HadesVR/HadesVR/docs/img/1.jpg

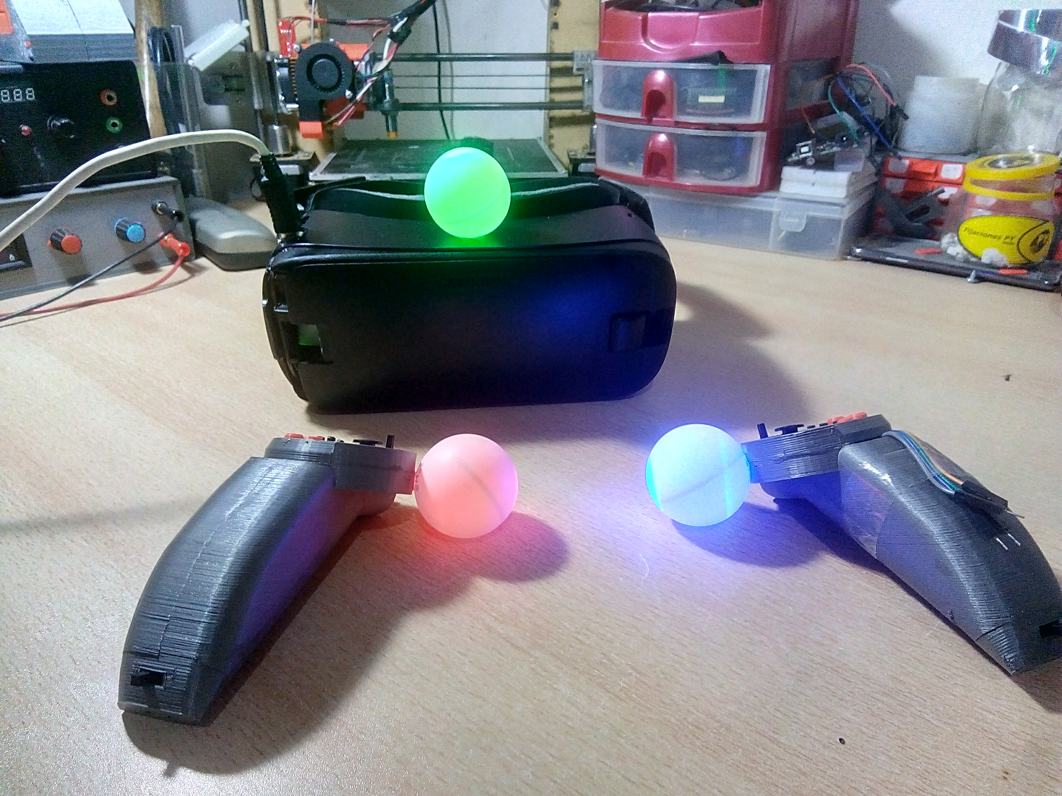
docs/img/1.jpg
