HadesVR/HadesVR/docs/img/2.jpg

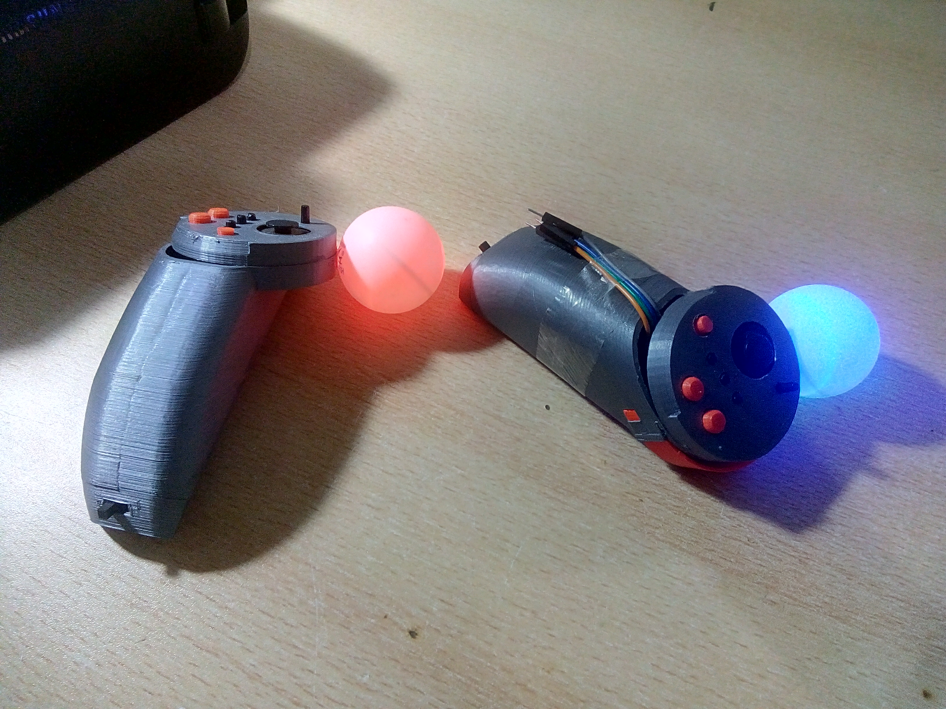
docs/img/2.jpg
