HadesVR/HadesVR/Software/Firmware/Controller_INDEX/Left_controller/Left_controller.ino

/*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
  The above copyright notice and this permission notice shall be included in all copies or substantial portions of the Software.

  THE SOFTWARE IS PROVIDED "AS IS", WITHOUT WARRANTY OF ANY KIND, EXPRESS OR IMPLIED,INCLUDING BUT NOT LIMITED TO
  THE WARRANTIES OF MERCHANTABILITY, FITNESS FOR A PARTICULAR PURPOSE AND NONINFRINGEMENT. IN NO EVENT SHALL THE
  AUTHORS OR COPYRIGHT HOLDERS BE LIABLE FOR ANY CLAIM, DAMAGES OR OTHER LIABILITY, WHETHER IN AN ACTION OF CONTRACT,
  TORT OR OTHERWISE, ARISING FROM, OUT OF OR IN CONNECTION WITH THE SOFTWARE OR THE USE OR OTHER DEALINGS IN THE SOFTWARE.
*/

#include <Wire.h>
#include <SPI.h>
#include <EEPROM.h>
#include "RF24.h"
#include "RegisterMap.h"

//==========================================================================================================
//************************************ USER CONFIGURABLE STUFF HERE*****************************************
//==========================================================================================================

#define MPU9250_ADDRESS     0x68            //ADO 0
#define CALPIN              5               //pin to start mag calibration at power on

#define APin                4
#define BPin                3
#define SysPin              5
#define FingerIndexPin      1
#define FingerMiddlePin     6
#define FingerRingPin       7
#define FingerPinkyPin      8
#define TrackpadPin         A0
#define JoyXPin             A1
#define JoyYPin             A2
#define JoyClickPin         2
#define TriggerPin          A3
#define VbatPin             A6

#define BatLevelMax         968             //you need to find all of these values on your own
#define JoyXMin             200             //check on the utils folder for sketches and instructions
#define JoyXMax             900             //that help on getting these values
#define JoyYMin             150             //YOU NEED TO DO THIS FOR BOTH CONTROLLERS
#define JoyYMax             870             //if you use these values without changing them you MAY
#define JoyXDeadZoneMin     515             //get stick drift
#define JoyXDeadZoneMax     590
#define JoyYDeadZoneMin     430
#define JoyYDeadZoneMax     560

//uint64_t Pipe = 0xF0F0F0F0E1LL; //right
uint64_t Pipe = 0xF0F0F0F0D2LL; //left
//==========================================================================================================


float magCalibration[3]; // factory mag calibration

struct Calibration {
  int calDone;
  float magBias[3];
  float magScale[3];
};
bool calDone;
Calibration cal;


static int ret;
static uint8_t fifoCount = 0;
struct s_quat {
  float w, x, y, z;
};

union u_quat {
  struct s_quat _f;
  long _l[4];
} q;

float magQuat[4] {1, 0, 0, 0};
float magHDG = 0;
float dmpHDG = 0;
float offsetHDG = 0;
float DMPquat[4];

static float mx, my, mz;
static short ax, ay, az;

enum class MFS { M14BITS, M16BITS }; // 0.6mG, 0.15mG per LSB
static float mRes;
MFS MFSSEL = MFS::M16BITS;

#define DMP_CODE_SIZE           (3062)
#define STARTADDRESS            0x0400
#define DMP_SAMPLE_RATE         (200)
const unsigned char dmp_memory[DMP_CODE_SIZE] PROGMEM = {
  /* bank # 0 */
  0x00, 0x00, 0x70, 0x00, 0x00, 0x00, 0x00, 0x24, 0x00, 0x00, 0x00, 0x02, 0x00, 0x03, 0x00, 0x00,
  0x00, 0x65, 0x00, 0x54, 0xff, 0xef, 0x00, 0x00, 0xfa, 0x80, 0x00, 0x0b, 0x12, 0x82, 0x00, 0x01,
  0x03, 0x0c, 0x30, 0xc3, 0x0e, 0x8c, 0x8c, 0xe9, 0x14, 0xd5, 0x40, 0x02, 0x13, 0x71, 0x0f, 0x8e,
  0x38, 0x83, 0xf8, 0x83, 0x30, 0x00, 0xf8, 0x83, 0x25, 0x8e, 0xf8, 0x83, 0x30, 0x00, 0xf8, 0x83,
  0xff, 0xff, 0xff, 0xff, 0x0f, 0xfe, 0xa9, 0xd6, 0x24, 0x00, 0x04, 0x00, 0x1a, 0x82, 0x79, 0xa1,
  0x00, 0x00, 0x00, 0x3c, 0xff, 0xff, 0x00, 0x00, 0x00, 0x10, 0x00, 0x00, 0x38, 0x83, 0x6f, 0xa2,
  0x00, 0x3e, 0x03, 0x30, 0x40, 0x00, 0x00, 0x00, 0x02, 0xca, 0xe3, 0x09, 0x3e, 0x80, 0x00, 0x00,
  0x20, 0x00, 0x00, 0x00, 0x00, 0x00, 0x00, 0x00, 0x40, 0x00, 0x00, 0x00, 0x60, 0x00, 0x00, 0x00,
  0x00, 0x0c, 0x00, 0x00, 0x00, 0x0c, 0x18, 0x6e, 0x00, 0x00, 0x06, 0x92, 0x0a, 0x16, 0xc0, 0xdf,
  0xff, 0xff, 0x02, 0x56, 0xfd, 0x8c, 0xd3, 0x77, 0xff, 0xe1, 0xc4, 0x96, 0xe0, 0xc5, 0xbe, 0xaa,
  0x00, 0x00, 0x00, 0x00, 0xff, 0xff, 0x0b, 0x2b, 0x00, 0x00, 0x16, 0x57, 0x00, 0x00, 0x03, 0x59,
  0x40, 0x00, 0x00, 0x00, 0x00, 0x00, 0x1d, 0xfa, 0x00, 0x02, 0x6c, 0x1d, 0x00, 0x00, 0x00, 0x00,
  0x3f, 0xff, 0xdf, 0xeb, 0x00, 0x3e, 0xb3, 0xb6, 0x00, 0x0d, 0x22, 0x78, 0x00, 0x00, 0x2f, 0x3c,
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
  radio.setPayloadSize(32);
  radio.setPALevel(RF24_PA_LOW);
  radio.setDataRate(RF24_2MBPS);
  radio.openWritingPipe(Pipe);
  radio.startListening();
  radio.setAutoAck(false);

  Wire.begin();

  if (readByte(MPU9250_ADDRESS, WHO_AM_I_MPU9250) == MPU9250_WHOAMI_DEFAULT_VALUE)
  {

    Serial.println("MPU9250 is online");
    initMPU();
    initDMP();
    if (readByte(AK8963_ADDRESS, AK8963_WHO_AM_I) == AK8963_WHOAMI_DEFAULT_VALUE)
    {
      Serial.println("AK8963 is online");
      initAK8963(magCalibration);
    }
    else
    {
      Serial.print("Could not connect to AK8963: 0x");
      Serial.println(readByte(AK8963_ADDRESS, AK8963_WHO_AM_I), HEX);
    }
  }
  else
  {
    Serial.print("Could not connect to MPU9250: 0x");
    Serial.println(readByte(MPU9250_ADDRESS, WHO_AM_I_MPU9250), HEX);
    while (true) {
      //      digitalWrite(PC13, LOW);
      delay(200);
      //     digitalWrite(PC13, HIGH);
      delay(200);
      //     digitalWrite(PC13, LOW);
      delay(200);
      //     digitalWrite(PC13, HIGH);
      delay(1000);
    }
  }

  EEPROM.get(0, cal);

  calDone = (cal.calDone != 99);                                  //check if calibration values are on flash
  while (calDone) {
    delay(200);
    if (!digitalRead(CALPIN)) {
      calDone = false;
    }
  }

  if (!digitalRead(CALPIN)) {                                        //enter calibration mode
    Serial.println("Magnetic calibration mode.");
    delay(1000);
    //    digitalWrite(PC13, LOW);
    magcalMPU9250(cal.magBias, cal.magScale);
    //    digitalWrite(PC13, HIGH);
    Serial.print("magBias: "); Serial.print(cal.magBias[0], 7); Serial.print(","); Serial.print(cal.magBias[1], 7); Serial.print(","); Serial.println(cal.magBias[2], 7);
    Serial.print("magScale: "); Serial.print(cal.magScale[0], 7); Serial.print(","); Serial.print(cal.magScale[1], 7); Serial.print(","); Serial.println(cal.magScale[2], 7);

    Serial.println("Writting calibration values to EEPROM!");
    cal.calDone = 99;
    EEPROM.put(0, cal);
    delay(3000);
  }

  //initialize controller data.
  data.qW = 1;
  data.qX = 0;
  data.qY = 0;
  data.qZ = 0;
  data.BTN = 0;
  data.trigg = 0;
  data.axisX = 0;
  data.axisY = 0;
  data.trackY = 0;
  data.vBAT = 0;
  data.fingerThumb = 0;
  data.fingerIndex = 0;
  data.fingerMiddle = 0;
  data.fingerRing = 0;
  data.fingerPinky = 0;
  data.Data = 0x633;

  /*
    data.Data |= 0x03;  //non diy index controller identifier
    data.Data |= 0x10;  //controller reports accelerometer values
    data.Data |= 0x20;  //controller does support hand tracking
    //data.Data |= 0x40;  //handtracking type is analog
    data.Data |= 0x200;  //controller color is blue (80 for blue 100 for green 200 for red)
    data.Data |= 0x400; //controller reports battery %
  */

}

void loop() {

  updateMPU();

  //Serial.print("qw: "); Serial.print(q._f.w); Serial.print(" qx: "); Serial.print(q._f.x); Serial.print(" qy: "); Serial.print(q._f.y); Serial.print(" qz: "); Serial.println(q._f.z);
  joyTouch = false;
  int btn = 0;
  tracky = analogRead(TrackpadPin);
  if (tracky > 560) {
    trackoutput = 1;
    btn |= IB_TrackpadTouch;
  }
  if (tracky < 300 && tracky > 100) {
    trackoutput = 0;
    btn |= IB_TrackpadTouch;
  }
  if (tracky == 0) {
    trackoutput = -1;
    btn |= IB_TrackpadTouch;
  }
  if (tracky < 550 && tracky > 400) {
    trackoutput = 0;
  }

  axisX = analogRead(JoyXPin);
  axisY = analogRead(JoyYPin);

  if (axisX > JoyXDeadZoneMax || axisX < JoyXDeadZoneMin) {
    data.axisX = map(axisX, JoyXMin, JoyXMax, -127, 127);
    btn |= IB_ThumbStickTouch;
    joyTouch = true;
  } else {
    data.axisX = 0;
  }

  if (axisY > JoyYDeadZoneMax || axisY < JoyYDeadZoneMin) {
    data.axisY = -map(axisY, JoyYMin, JoyYMax, -127, 127);
    btn |= IB_ThumbStickTouch;
    joyTouch = true;
  } else {
    data.axisY = 0;
  }


  if (analogRead(TriggerPin) < 1000) {
    data.trigg = map(analogRead(TriggerPin), 1024, 0, 0, 255);
    data.fingerIndex = map(analogRead(TriggerPin), 1024, 0, 0, 255);
  }
  else {
    data.trigg = 0;
    data.fingerIndex = 0;
  }


  if (!digitalRead(APin)) {
    btn |= IB_AClick;
    btn |= IB_ATouch;
  }
  if (!digitalRead(BPin)) {
    btn |= IB_BClick;
    btn |= IB_BTouch;
  }
  if (!digitalRead(SysPin)) {
    btn |= IB_SYSClick;
  }
  if (!digitalRead(JoyClickPin)) {
    btn |= IB_ThumbStickClick;
  }
  //  if (digitalRead(FingerIndexPin)) {
  //    data.fingerIndex = 255;
  //  }
  //  else {
  //    data.fingerIndex = 0;
  //  }
  if (digitalRead(FingerMiddlePin)) {
    data.fingerMiddle = 255;
  }
  else {
    data.fingerMiddle = 0;
  }
  if (digitalRead(FingerRingPin)) {
    data.fingerRing = 255;
  }
  else {
    data.fingerRing = 0;
  }
  if (digitalRead(FingerPinkyPin)) {
    data.fingerPinky = 255;
  }
  else {
    data.fingerPinky = 0;
  }


  data.BTN = btn;
  data.trackY = (trackoutput * 127);
  data.vBAT = (map(analogRead(VbatPin), 787, BatLevelMax, 0, 255));
  data.qW = (int16_t)(q._f.w * 32767.f);
  data.qX = (int16_t)(q._f.y * 32767.f);
  data.qY = (int16_t)(q._f.z * 32767.f);
  data.qZ = (int16_t)(q._f.x * 32767.f);
  data.accX = ax;
  data.accY = ay;
  data.accZ = az;
  radio.stopListening();
  radio.write(&data, sizeof(ctrlData));
  radio.startListening();
}


void initMPU()
{
  unsigned char data;
  // reset device
  writeByte(MPU9250_ADDRESS, PWR_MGMT_1, 0x80);
  // wake up device
  writeByte(MPU9250_ADDRESS, PWR_MGMT_1, 0x00); // Clear sleep mode bit (6), enable all sensors
  delay(100); // Wait for all registers to reset

  writeByte(MPU9250_ADDRESS, MPU_CONFIG, 0x03); //set lpf to 42hz

  // get stable time source
  writeByte(MPU9250_ADDRESS, PWR_MGMT_1, 0x01);  // Auto select clock source to be PLL gyroscope reference if ready else
  delay(200);

  //enable all sensors
  writeByte(MPU9250_ADDRESS, PWR_MGMT_2, 0x00);
  delay(200);

  data = 3 << 3; // 11 = 2000dps
  writeByte(MPU9250_ADDRESS, GYRO_CONFIG, data);

  data = 1 << 3; // 01 = 4g
  writeByte(MPU9250_ADDRESS, ACCEL_CONFIG, data);
  // Set sample rate = gyroscope output rate/(1 + SMPLRT_DIV)
  writeByte(MPU9250_ADDRESS, SMPLRT_DIV, 0x04);  // Use a 200 Hz rate; a rate consistent with the filter update rate


  data = 0x01;          //BIT_DRDY_EN
  writeByte(MPU9250_ADDRESS, INT_ENABLE, data);
  // Configure Interrupts and Bypass Enable
  // Set interrupt pin active high, push-pull, hold interrupt pin level HIGH until interrupt cleared,
  // clear on read of INT_STATUS, and enable I2C_BYPASS_EN so additional chips
  // can join the I2C bus and all can be controlled by the Arduino as master
  writeByte(MPU9250_ADDRESS, INT_PIN_CFG, 0x22);
  delay(100);
}

void initDMP()
{
  dmpLoadFirmware(DMP_CODE_SIZE, dmp_memory, STARTADDRESS, DMP_SAMPLE_RATE);
  ret = dmp_set_fifo_rate(200);
  ret = enableDMP();
  ret = dmp_enable_features();
}

void initAK8963(float * destination)
{
  // First extract the factory calibration for each magnetometer axis
  uint8_t rawData[3];  // x/y/z gyro calibration data stored here
  writeByte(AK8963_ADDRESS, AK8963_CNTL, 0x00); // Power down magnetometer
  delay(10);
  writeByte(AK8963_ADDRESS, AK8963_CNTL, 0x0F); // Enter Fuse ROM access mode
  delay(10);
  readBytes(AK8963_ADDRESS, AK8963_ASAX, 3, &rawData[0]);  // Read the x-, y-, and z-axis calibration values
  destination[0] =  (float)(rawData[0] - 128) / 256. + 1.; // Return x-axis sensitivity adjustment values, etc.
  destination[1] =  (float)(rawData[1] - 128) / 256. + 1.;
  destination[2] =  (float)(rawData[2] - 128) / 256. + 1.;
  writeByte(AK8963_ADDRESS, AK8963_CNTL, 0x00); // Power down magnetometer
  delay(10);
  // Configure the magnetometer for continuous read and highest resolution
  // set Mscale bit 4 to 1 (0) to enable 16 (14) bit resolution in CNTL register,
  // and enable continuous mode data acquisition Mmode (bits [3:0]), 0010 for 8 Hz and 0110 for 100 Hz sample rates
  writeByte(AK8963_ADDRESS, AK8963_CNTL, (uint8_t)MFSSEL << 4 | Mmode); // Set magnetometer data resolution and sample ODR
  delay(10);

  //  Serial.println("Calibration values: ");
  //  Serial.print("X-Axis sensitivity adjustment value "); Serial.println(destination[0], 2);
  //  Serial.print("Y-Axis sensitivity adjustment value "); Serial.println(destination[1], 2);
  //  Serial.print("Z-Axis sensitivity adjustment value "); Serial.println(destination[2], 2);
  //  Serial.print("X-Axis sensitivity offset value "); Serial.println(cal.magBias[0], 2);
  //  Serial.print("Y-Axis sensitivity offset value "); Serial.println(cal.magBias[1], 2);
  //  Serial.print("Z-Axis sensitivity offset value "); Serial.println(cal.magBias[2], 2);
}

void magcalMPU9250(float * dest1, float * dest2)
{
  uint16_t ii = 0, sample_count = 0;
  int32_t mag_bias[3] = {0, 0, 0}, mag_scale[3] = {0, 0, 0};
  int16_t mag_max[3] = { -32767, -32767, -32767}, mag_min[3] = {32767, 32767, 32767}, mag_temp[3] = {0, 0, 0};

  Serial.println("Mag Calibration: Wave device in a figure eight until done!");
  delay(4000);

  // shoot for ~fifteen seconds of mag data
  if      (Mmode == 0x02) sample_count = 128;  // at 8 Hz ODR, new mag data is available every 125 ms
  else if (Mmode == 0x06) sample_count = 1500;  // at 100 Hz ODR, new mag data is available every 10 ms

  for (ii = 0; ii < sample_count; ii++)
  {
    uint8_t rawData[7];  // x/y/z gyro register data, ST2 register stored here, must read ST2 at end of data acquisition
    if (readByte(AK8963_ADDRESS, AK8963_ST1) & 0x01) { // wait for magnetometer data ready bit to be set
      readBytes(AK8963_ADDRESS, AK8963_XOUT_L, 7, &rawData[0]);  // Read the six raw data and ST2 registers sequentially into data array
      uint8_t c = rawData[6]; // End data read by reading ST2 register
      if (!(c & 0x08)) { // Check if magnetic sensor overflow set, if not then report data
        mag_temp[0] = ((int16_t)rawData[1] << 8) | rawData[0];  // Turn the MSB and LSB into a signed 16-bit value
        mag_temp[1] = ((int16_t)rawData[3] << 8) | rawData[2];  // Data stored as little Endian
        mag_temp[2] = ((int16_t)rawData[5] << 8) | rawData[4];
      }
    }
    for (int jj = 0; jj < 3; jj++)
    {
      if (mag_temp[jj] > mag_max[jj]) mag_max[jj] = mag_temp[jj];
      if (mag_temp[jj] < mag_min[jj]) mag_min[jj] = mag_temp[jj];
    }
    if (Mmode == 0x02) delay(135); // at 8 Hz ODR, new mag data is available every 125 ms
    if (Mmode == 0x06) delay(12); // at 100 Hz ODR, new mag data is available every 10 ms
  }
  //
  //  Serial.println("mag x min/max:"); Serial.println(mag_max[0]); Serial.println(mag_min[0]);
  //  Serial.println("mag y min/max:"); Serial.println(mag_max[1]); Serial.println(mag_min[1]);
  //  Serial.println("mag z min/max:"); Serial.println(mag_max[2]); Serial.println(mag_min[2]);

  // Get hard iron correction
  mag_bias[0]  = (mag_max[0] + mag_min[0]) / 2; // get average x mag bias in counts
  mag_bias[1]  = (mag_max[1] + mag_min[1]) / 2; // get average y mag bias in counts
  mag_bias[2]  = (mag_max[2] + mag_min[2]) / 2; // get average z mag bias in counts

  dest1[0] = (float) mag_bias[0] * mRes * magCalibration[0]; // save mag biases in G for main program
  dest1[1] = (float) mag_bias[1] * mRes * magCalibration[1];
  dest1[2] = (float) mag_bias[2] * mRes * magCalibration[2];

  // Get soft iron correction estimate
  mag_scale[0]  = (mag_max[0] - mag_min[0]) / 2; // get average x axis max chord length in counts
  mag_scale[1]  = (mag_max[1] - mag_min[1]) / 2; // get average y axis max chord length in counts
  mag_scale[2]  = (mag_max[2] - mag_min[2]) / 2; // get average z axis max chord length in counts

  float avg_rad = mag_scale[0] + mag_scale[1] + mag_scale[2];
  avg_rad /= 3.0;

  dest2[0] = avg_rad / ((float)mag_scale[0]);
  dest2[1] = avg_rad / ((float)mag_scale[1]);
  dest2[2] = avg_rad / ((float)mag_scale[2]);

  Serial.println("Mag Calibration done!");

  //  Serial.println("AK8963 mag biases (mG)");
  //  Serial.print(cal.magBias[0]); Serial.print(", ");
  //  Serial.print(cal.magBias[1]); Serial.print(", ");
  //  Serial.print(cal.magBias[2]); Serial.println();
  //  Serial.println("AK8963 mag scale (mG)");
  //  Serial.print(cal.magScale[0]); Serial.print(", ");
  //  Serial.print(cal.magScale[1]); Serial.print(", ");
  //  Serial.print(cal.magScale[2]); Serial.println();
}

void updateMag()
{
  if (readByte(AK8963_ADDRESS, AK8963_ST1) & 0x01) {             // wait for magnetometer data ready bit to be set
    int16_t magCount[3] = {0, 0, 0};                             // Stores the 16-bit signed magnetometer sensor output
    uint8_t rawData[7];                                          // x/y/z gyro register data, ST2 register stored here, must read ST2 at end of data acquisition
    readBytes(AK8963_ADDRESS, AK8963_XOUT_L, 7, &rawData[0]);    // Read the six raw data and ST2 registers sequentially into data array
    uint8_t c = rawData[6];                                      // End data read by reading ST2 register
    if (!(c & 0x08)) {                                           // Check if magnetic sensor overflow set, if not then report data
      magCount[0] = ((int16_t)rawData[1] << 8) | rawData[0];     // Turn the MSB and LSB into a signed 16-bit value
      magCount[1] = ((int16_t)rawData[3] << 8) | rawData[2];     // Data stored as little Endian
      magCount[2] = ((int16_t)rawData[5] << 8) | rawData[4];
    }

    // getMres();
    // Calculate the magnetometer values in milliGauss
    // Include factory calibration per data sheet and user environmental corrections

    mx = (float)(magCount[0] * mRes * magCalibration[0] - cal.magBias[0]) * cal.magScale[0];  // get actual magnetometer value, this depends on scale being set
    my = (float)(magCount[1] * mRes * magCalibration[1] - cal.magBias[1]) * cal.magScale[1];
    mz = (float)(magCount[2] * mRes * magCalibration[2] - cal.magBias[2]) * cal.magScale[2];

  }
}

float getMres()
{
  switch (MFSSEL)
  {
    // Possible magnetometer scales (and their register bit settings) are:
    // 14 bit resolution (0) and 16 bit resolution (1)
    // Proper scale to return milliGauss
    case MFS::M14BITS: return 10. * 4912. / 8190.0;
    case MFS::M16BITS: return 10. * 4912. / 32760.0;
  }
}

void mpu_reset_fifo()
{
  unsigned char data;

  data = 0;

  //reset registers
  writeByte(MPU9250_ADDRESS, INT_ENABLE, data);

  writeByte(MPU9250_ADDRESS, FIFO_EN, data);

  writeByte(MPU9250_ADDRESS, USER_CTRL, data);

  //reset FIFO and DMP
  data = 0x04 | 0x08;   //BIT_FIFO_RST, BIT_DMP_RST
  writeByte(MPU9250_ADDRESS, USER_CTRL, data);

  delay(50);

  //Enable them
  data = 0x80 | 0x40;   //BIT_DMP_EN, BIT_FIFO_EN
  writeByte(MPU9250_ADDRESS, USER_CTRL, data);

  data = 0x02;          //BIT_DMP_INT_EN
  writeByte(MPU9250_ADDRESS, INT_ENABLE, data);

  data = 0;
  writeByte(MPU9250_ADDRESS, FIFO_EN, data);

}

int updateMPU()
{
  do {
    //Read DMP
    ret = readDMP(q._l);

    if (ret != 0) return ret;
  } while (fifoCount > 1);

  //Convert to float
#define QUAT_SENS       1073741824.f //2^30
  DMPquat[0] = (float)q._l[0] / (float)QUAT_SENS;
  DMPquat[1] = (float)q._l[1] / (float)QUAT_SENS;
  DMPquat[2] = (float)q._l[2] / (float)QUAT_SENS;
  DMPquat[3] = (float)q._l[3] / (float)QUAT_SENS;

  float newOffset;
  float tmp;

  //Apply offsets.
  q._f.w = magQuat[0] * DMPquat[0] - magQuat[3] * DMPquat[3];
  q._f.x = magQuat[0] * DMPquat[1] - magQuat[3] * DMPquat[2];
  q._f.y = magQuat[0] * DMPquat[2] + magQuat[3] * DMPquat[1];
  q._f.z = magQuat[0] * DMPquat[3] + magQuat[3] * DMPquat[0];

  tmp = invSqrt(q._f.w * q._f.w + q._f.x * q._f.x + q._f.y * q._f.y + q._f.z * q._f.z);
  q._f.w *= tmp;
  q._f.y *= tmp;
  q._f.x *= tmp;
  q._f.z *= tmp;

  if (DMPquat[1] > -0.03f && DMPquat[1] < 0.03f && DMPquat[2] > -0.04f && DMPquat[2] < 0.04f && !joyTouch)   //get a new offset if relatively level
  {
    updateMag();

    double siny_cosp = 2 * (DMPquat[0] * DMPquat[3] + DMPquat[1] * DMPquat[2]);
    double cosy_cosp = 1 - 2 * (DMPquat[2] * DMPquat[2] + DMPquat[3] * DMPquat[3]);

    magHDG = atan2(my , mx);
    dmpHDG = atan2(siny_cosp, cosy_cosp);

    newOffset = (magHDG - dmpHDG);

    tmp = (newOffset - offsetHDG);

#ifdef SERIAL_DEBUG
    Serial.print("wanna get to ");
    Serial.print(magHDG * 180 / M_PI);
    Serial.print(" have ");
    Serial.print(dmpHDG * 180 / M_PI);
    Serial.print(" which is a ");
    Serial.print(newOffset * 180 / M_PI);
    Serial.print(" difference, and to get to that I'll need to add ");
    Serial.print(tmp * 180 / M_PI);
    Serial.print(" to ");
    Serial.print(offsetHDG * 180 / M_PI);
#endif

    if (tmp > M_PI) {                  //wrap around
      tmp -= (M_PI * 2);
    }
    if (tmp < -M_PI) {
      tmp += (M_PI * 2);
    }

    if (tmp > -0.08f && tmp < 0.08f)    //go slower for slower distances to even out the jittery magnetometer output
    {
      offsetHDG += tmp * 0.02f;
    }
    else if (tmp > -0.17f && tmp < 0.17f)
    {
      offsetHDG += tmp * 0.04f;
    }
    else if (tmp > -0.26f && tmp < 0.26f)
    {
      offsetHDG += tmp * 0.1f;
    }
    else
    {
      offsetHDG += tmp;                 //go fast if distance target is too far off.
    }


    if (offsetHDG > M_PI) {             //wrap around
      offsetHDG -= (M_PI * 2);
    }
    if (offsetHDG < -M_PI) {
      offsetHDG += (M_PI * 2);
    }

    magQuat[0] = cos(offsetHDG / 2);    //get quaternion
    magQuat[3] = sin(offsetHDG / 2);

#ifdef SERIAL_DEBUG

    siny_cosp = 2 * (q._f.w * q._f.z + q._f.x * q._f.y);
    cosy_cosp = 1 - 2 * (q._f.y * q._f.y + q._f.z * q._f.z);

    dmpHDG = atan2(siny_cosp, cosy_cosp);
    Serial.print(" offset for an ouput of ");
    Serial.println(dmpHDG * 180 / M_PI);

#endif
  }
}

int readDMP(long *quat)
{
  unsigned short fifo_count;
  unsigned char fifo_data[32];
  unsigned char ii = 0;
  unsigned char tmp[2];
  short accel[3];

  /* Get a packet. */
  readBytes(MPU9250_ADDRESS, FIFO_COUNTH, 2, tmp);
  fifo_count = (tmp[0] << 8) | tmp[1];
  if (fifo_count < 28) {      //no packet available.
    fifoCount = 0;
    return 1;
  }
  if (fifo_count > (1024 >> 1)) {
    /* FIFO is 50% full, better check overflow bit. */
    readBytes(MPU9250_ADDRESS, INT_STATUS, 1, tmp);
    if (tmp[0] & 0x10) {      //if fifo overflow
      mpu_reset_fifo();       //reset fifo
      return 2;
    }
  }

  readBytes(MPU9250_ADDRESS, FIFO_R_W, 28, fifo_data);
  fifoCount = (uint8_t)(fifo_count / 28 - 1);

  /* Parse DMP packet. */

  quat[0] = ((long)fifo_data[0] << 24) | ((long)fifo_data[1] << 16) |
            ((long)fifo_data[2] << 8) | fifo_data[3];
  quat[1] = ((long)fifo_data[4] << 24) | ((long)fifo_data[5] << 16) |
            ((long)fifo_data[6] << 8) | fifo_data[7];
  quat[2] = ((long)fifo_data[8] << 24) | ((long)fifo_data[9] << 16) |
            ((long)fifo_data[10] << 8) | fifo_data[11];
  quat[3] = ((long)fifo_data[12] << 24) | ((long)fifo_data[13] << 16) |
            ((long)fifo_data[14] << 8) | fifo_data[15];
  ii += 16;

  ay = ((short)fifo_data[ii + 0] << 8) | fifo_data[ii + 1];
  ax = ((short)fifo_data[ii + 2] << 8) | fifo_data[ii + 3];
  az = ((short)fifo_data[ii + 4] << 8) | fifo_data[ii + 5];
  ii += 6;
  /*
    ax = (float)accel[1] * 4.0 / 32768.0;
    ay = (float)accel[0] * 4.0 / 32768.0;
    az = (float)accel[2] * 4.0 / 32768.0;
  */
  return 0;
}

int dmp_set_fifo_rate(unsigned short rate)
{
  const unsigned char regs_end[12] = {0xfe, 0xf2, 0xab,
                                      0xc4, 0xaa, 0xf1, 0xdf, 0xdf, 0xBB, 0xAF, 0xdf, 0xdf
                                     };
  unsigned short div;
  unsigned char tmp[8];

  if (rate > DMP_SAMPLE_RATE)
    return -1;
  div = DMP_SAMPLE_RATE / rate - 1;
  tmp[0] = (unsigned char)((div >> 8) & 0xFF);
  tmp[1] = (unsigned char)(div & 0xFF);
  if (mpu_write_mem(22 + 512, 2, tmp))
    return -1;
  if (mpu_write_mem(2753, 12, (unsigned char*)regs_end))
    return -1;

  return 0;
}

int enableDMP()
{
  unsigned char tmp;
  /* Disable data ready interrupt. */
  tmp = 0x00;
  writeByte(MPU9250_ADDRESS, INT_ENABLE, tmp);
  /* Remove FIFO elements. */
  tmp = 0;
  writeByte(MPU9250_ADDRESS, 0x23, tmp);
  /* Enable DMP interrupt. */
  tmp = 0x02;
  writeByte(MPU9250_ADDRESS, INT_ENABLE, tmp);

  mpu_reset_fifo();

  return 0;
}

int dmp_enable_features()
{
#define GYRO_SF             (46850825LL * 200 / DMP_SAMPLE_RATE)
  unsigned char tmp[10];

  /* TODO: All of these settings can probably be integrated into the default
     DMP image.
  */
  /* Set integration scale factor. */
  tmp[0] = (unsigned char)((GYRO_SF >> 24) & 0xFF);
  tmp[1] = (unsigned char)((GYRO_SF >> 16) & 0xFF);
  tmp[2] = (unsigned char)((GYRO_SF >> 8) & 0xFF);
  tmp[3] = (unsigned char)(GYRO_SF & 0xFF);
  mpu_write_mem(104, 4, tmp);

  /* Send sensor data to the FIFO. */
  tmp[0] = 0xA3;
  tmp[1] = 0xC0;
  tmp[2] = 0xC8;
  tmp[3] = 0xC2;
  tmp[4] = 0xC4;
  tmp[5] = 0xCC;
  tmp[6] = 0xC6;
  tmp[7] = 0xA3;
  tmp[8] = 0xA3;
  tmp[9] = 0xA3;
  mpu_write_mem(2727, 10, tmp);

  /* Send gesture data to the FIFO. */
  tmp[0] = 0xD8;
  mpu_write_mem(2742, 1, tmp);

  //enable DMP gyro CAL
  unsigned char regs1[9] = {0xb8, 0xaa, 0xb3, 0x8d, 0xb4, 0x98, 0x0d, 0x35, 0x5d};
  mpu_write_mem(1208, 9, regs1);

  tmp[0] = 0xB2;
  tmp[1] = 0x8B;
  tmp[2] = 0xB6;
  tmp[3] = 0x9B;

  mpu_write_mem(2722, 4, tmp);

  unsigned char regs2[4];

  regs2[0] = 0x20;
  regs2[1] = 0x28;
  regs2[2] = 0x30;
  regs2[3] = 0x38;

  mpu_write_mem(2718, 4, regs2);

  mpu_reset_fifo();

  return 0;
}

void dmpLoadFirmware(unsigned short length, const unsigned char *firmware, unsigned short start_addr, unsigned short sample_rate) {
  unsigned short ii;
  unsigned short this_write;
  int errCode;
  uint8_t *progBuffer;
  /* Must divide evenly into st->hw->bank_size to avoid bank crossings. */
#define LOAD_CHUNK  (16)
  unsigned char cur[LOAD_CHUNK], tmp[2];

  progBuffer = (uint8_t *)malloc(LOAD_CHUNK);
  for (ii = 0; ii < length; ii += this_write) {
    this_write = min(LOAD_CHUNK, length - ii);

    for (int progIndex = 0; progIndex < this_write; progIndex++)

      progBuffer[progIndex] = pgm_read_byte(firmware + ii + progIndex);


    mpu_write_mem(ii, this_write, progBuffer);

    mpu_read_mem(ii, this_write, cur);


    if (memcmp(progBuffer, cur, this_write)) {
      Serial.println("oh shit something's wrong with the DMP's firmware (memcmp)");
    }
  }

  /* Set program start address. */
  tmp[0] = start_addr >> 8;
  tmp[1] = start_addr & 0xFF;
  writeBytes(MPU9250_ADDRESS, 0x70, 2, tmp);

}

int mpu_write_mem(unsigned short mem_addr, unsigned short length,
                  unsigned char *data)
{
  unsigned char tmp[2];

  if (!data)
    return -1;

  tmp[0] = (unsigned char)(mem_addr >> 8);
  tmp[1] = (unsigned char)(mem_addr & 0xFF);

  /* Check bank boundaries. */
  if (tmp[1] + length > 256)
    return -2;


  writeBytes(MPU9250_ADDRESS, 0x6D, 2, tmp);

  writeBytes(MPU9250_ADDRESS, 0x6F, length, data);

  return 0;
}

int mpu_read_mem(unsigned short mem_addr, unsigned short length,
                 unsigned char *data)
{
  unsigned char tmp[2];

  if (!data)
    return -1;

  tmp[0] = (unsigned char)(mem_addr >> 8);
  tmp[1] = (unsigned char)(mem_addr & 0xFF);

  /* Check bank boundaries. */
  if (tmp[1] + length > 256)
    return -2;

  writeBytes(MPU9250_ADDRESS, 0x6D, 2, tmp);

  readBytes(MPU9250_ADDRESS, 0x6F, length, data);

  return 0;
}

uint8_t readByte(uint8_t address, uint8_t subAddress)
{
  uint8_t data; // `data` will store the register data
  Wire.beginTransmission(address);         // Initialize the Tx buffer
  Wire.write(subAddress);                  // Put slave register address in Tx buffer
  Wire.endTransmission(false);             // Send the Tx buffer, but send a restart to keep connection alive
  Wire.requestFrom(address, (uint8_t) 1);  // Read one byte from slave register address
  data = Wire.read();                      // Fill Rx buffer with result
  return data;                             // Return data read from slave register
}

void readBytes(uint8_t address, uint8_t subAddress, uint8_t count, uint8_t * dest)
{
  Wire.beginTransmission(address);   // Initialize the Tx buffer
  Wire.write(subAddress);            // Put slave register address in Tx buffer
  Wire.endTransmission(false);       // Send the Tx buffer, but send a restart to keep connection alive
  uint8_t i = 0;
  Wire.requestFrom(address, count);  // Read bytes from slave register address
  while (Wire.available()) {
    dest[i++] = Wire.read();
  }         // Put read results in the Rx buffer
}

void writeByte(uint8_t address, uint8_t subAddress, uint8_t data)
{
  Wire.beginTransmission(address);  // Initialize the Tx buffer
  Wire.write(subAddress);           // Put slave register address in Tx buffer
  Wire.write(data);                 // Put data in Tx buffer
  Wire.endTransmission();           // Send the Tx buffer
}

void writeBytes(uint8_t address, uint8_t subAddress, uint8_t count, uint8_t* data) {

  Wire.beginTransmission(address);
  Wire.write((uint8_t) subAddress); // send address
  for (uint8_t i = 0; i < count; i++) {
    Wire.write((uint8_t) data[i]);
  }
  Wire.endTransmission();
}
//fast invsqrt
float invSqrt(float x) {
  float halfx = 0.5f * x;
  float y = x;
  long i = *(long*)&y;
  i = 0x5f3759df - (i >> 1);
  y = *(float*)&i;
  y = y * (1.5f - (halfx * y * y));
  y = y * (1.5f - (halfx * y * y));
  return y;
}
