HadesVR/HadesVR/Software/Driver/src/samples/driver_HadesVR/driver_main.cpp

//============ Copyright (c) Valve Corporation, All rights reserved. ============

#include <openvr_driver.h>
#include "driverlog.h"


#include <vector>
#include <thread>
#include <chrono>

#include <windows.h>
#include <atlbase.h>
#include <atlstr.h> 
#include "dataHandler.h"
#include "devices.hpp"
#include "settingsAPIKeys.h"

using namespace vr;
using namespace std::chrono;

#if defined(_WIN32)
#define HMD_DLL_EXPORT extern "C" __declspec( dllexport )
#define HMD_DLL_IMPORT extern "C" __declspec( dllimport )
#elif defined(__GNUC__) || defined(COMPILER_GCC) || defined(__APPLE__)
#define HMD_DLL_EXPORT extern "C" __attribute__((visibility("default")))
#define HMD_DLL_IMPORT extern "C" 
#else
#error "Unsupported Platform."
#endif

inline HmdQuaternion_t HmdQuaternion_Init( double w, double x, double y, double z )
{
	HmdQuaternion_t quat;
	quat.w = w;
	quat.x = x;
	quat.y = y;
	quat.z = z;
	return quat;
}


inline vr::HmdQuaternion_t retquat(double qW, double qX, double qY, double qZ)
{
	vr::HmdQuaternion_t q;
	// Abbreviations for the various angular functions
	q.w = qW;
	q.x = qX;
	q.y = qY;
	q.z = qZ;

	return q;
}


inline void HmdMatrix_SetIdentity( HmdMatrix34_t *pMatrix )
{
	pMatrix->m[0][0] = 1.f;
	pMatrix->m[0][1] = 0.f;
	pMatrix->m[0][2] = 0.f;
	pMatrix->m[0][3] = 0.f;
	pMatrix->m[1][0] = 0.f;
	pMatrix->m[1][1] = 1.f;
	pMatrix->m[1][2] = 0.f;
	pMatrix->m[1][3] = 0.f;
	pMatrix->m[2][0] = 0.f;
	pMatrix->m[2][1] = 0.f;
	pMatrix->m[2][2] = 1.f;
	pMatrix->m[2][3] = 0.f;
}


#define SUCCESS 0
#define FAILURE 1

HMODULE hDll;

THMD HMDdata;

bool HMDConnected = false, ctrlsConnected = false, trackersConnected = false;

int controllerMode, trackerMode;

double DegToRad(double f) {
	return f * (3.14159265358979323846 / 180);
}

int comPort = 3;
//Velocity
double FirstCtrlLastPos[3] = { 0, 0, 0 }, SecondCtrlLastPos[3] = { 0, 0, 0 };
double TrackerWaistLastPos[3] = { 0, 0, 0 }, TrackerLeftFootLastPos[3] = { 0, 0, 0 }, TrackerRightFootLastPos[3] = { 0, 0, 0 };

milliseconds deltaTime;

//-----------------------------------------------------------------------------
// Purpose: HMD mess over here
//-----------------------------------------------------------------------------

class C_HMDDeviceDriver : public vr::ITrackedDeviceServerDriver, public vr::IVRDisplayComponent
{
public:
	C_HMDDeviceDriver(  )
	{
		HMDIndex_t = vr::k_unTrackedDeviceIndexInvalid;
		m_ulPropertyContainer = vr::k_ulInvalidPropertyContainer;

		//DriverLog( "Using settings values\n" );
		m_flIPD = vr::VRSettings()->GetFloat(k_pch_Display_Section, k_pch_Sample_IPD_Float);

		char buf[1024];
		vr::VRSettings()->GetString( k_pch_Driver_Section, k_pch_Sample_SerialNumber_String, buf, sizeof( buf ) );
		m_sSerialNumber = buf;

		vr::VRSettings()->GetString( k_pch_Driver_Section, k_pch_Sample_ModelNumber_String, buf, sizeof( buf ) );
		m_sModelNumber = buf;

		m_nWindowX = vr::VRSettings()->GetInt32( k_pch_Display_Section, k_pch_Sample_WindowX_Int32 );
		m_nWindowY = vr::VRSettings()->GetInt32( k_pch_Display_Section, k_pch_Sample_WindowY_Int32 );
		m_nWindowWidth = vr::VRSettings()->GetInt32( k_pch_Display_Section, k_pch_Sample_WindowWidth_Int32 );
		m_nWindowHeight = vr::VRSettings()->GetInt32( k_pch_Display_Section, k_pch_Sample_WindowHeight_Int32 );
		m_nRenderWidth = vr::VRSettings()->GetInt32( k_pch_Display_Section, k_pch_Sample_RenderWidth_Int32 );
		m_nRenderHeight = vr::VRSettings()->GetInt32( k_pch_Display_Section, k_pch_Sample_RenderHeight_Int32 );
		m_flSecondsFromVsyncToPhotons = vr::VRSettings()->GetFloat( k_pch_Display_Section, k_pch_Sample_SecondsFromVsyncToPhotons_Float );
		m_flDisplayFrequency = vr::VRSettings()->GetFloat( k_pch_Display_Section, k_pch_Sample_DisplayFrequency_Float );
		m_fDistortionK1 = vr::VRSettings()->GetFloat(k_pch_Display_Section, k_pch_Sample_DistortionK1_Float);
		m_fDistortionK2 = vr::VRSettings()->GetFloat(k_pch_Display_Section, k_pch_Sample_DistortionK2_Float);
		m_fZoomWidth = vr::VRSettings()->GetFloat(k_pch_Display_Section, k_pch_Sample_ZoomWidth_Float);
		m_fZoomHeight = vr::VRSettings()->GetFloat(k_pch_Display_Section, k_pch_Sample_ZoomHeight_Float);
		m_fFOV = (vr::VRSettings()->GetFloat(k_pch_Display_Section, k_pch_Sample_FOV_Float) * 3.14159265358979323846 / 180); //radians
		m_nDistanceBetweenEyes = vr::VRSettings()->GetInt32(k_pch_Display_Section, k_pch_Sample_DistanceBetweenEyes_Int32);
		m_nScreenOffsetX = vr::VRSettings()->GetInt32(k_pch_Display_Section, k_pch_Sample_ScreenOffsetX_Int32);
		m_nScreenOffsetY = vr::VRSettings()->GetInt32(k_pch_Display_Section, k_pch_Sample_ScreenOffsetY_Int32);
		m_bStereoMode = vr::VRSettings()->GetBool(k_pch_Display_Section, k_pch_Sample_Stereo_Bool);
		m_bDebugMode = vr::VRSettings()->GetBool(k_pch_Display_Section, k_pch_Sample_DebugMode_Bool);
		m_displayOnDesktop = vr::VRSettings()->GetBool(k_pch_Display_Section, k_pch_Sample_DisplayOnDesktop);
		m_displayReal = vr::VRSettings()->GetBool(k_pch_Display_Section, k_pch_Sample_DisplayReal);
		
		DriverLog( "Window: %d %d %d %d\n", m_nWindowX, m_nWindowY, m_nWindowWidth, m_nWindowHeight );
		DriverLog( "Render Target: %d %d\n", m_nRenderWidth, m_nRenderHeight );
		DriverLog( "Seconds from Vsync to Photons: %f\n", m_flSecondsFromVsyncToPhotons );
		DriverLog( "Display Frequency: %f\n", m_flDisplayFrequency );
		DriverLog( "IPD: %f\n", m_flIPD );
	}

	virtual ~C_HMDDeviceDriver()
	{
	}


	virtual EVRInitError Activate( vr::TrackedDeviceIndex_t unObjectId ) 
	{	
		HMDIndex_t = unObjectId;
		m_ulPropertyContainer = vr::VRProperties()->TrackedDeviceToPropertyContainer( HMDIndex_t );

		vr::VRProperties()->SetStringProperty( m_ulPropertyContainer, Prop_ModelNumber_String, m_sModelNumber.c_str() );
		vr::VRProperties()->SetStringProperty( m_ulPropertyContainer, Prop_RenderModelName_String, m_sModelNumber.c_str() );
		vr::VRProperties()->SetFloatProperty( m_ulPropertyContainer, Prop_UserIpdMeters_Float, m_flIPD );
		vr::VRProperties()->SetFloatProperty( m_ulPropertyContainer, Prop_UserHeadToEyeDepthMeters_Float, 0.f );
		vr::VRProperties()->SetFloatProperty( m_ulPropertyContainer, Prop_DisplayFrequency_Float, m_flDisplayFrequency );
		vr::VRProperties()->SetFloatProperty( m_ulPropertyContainer, Prop_SecondsFromVsyncToPhotons_Float, m_flSecondsFromVsyncToPhotons );

		
		vr::VRProperties()->SetUint64Property( m_ulPropertyContainer, Prop_CurrentUniverseId_Uint64, 2 );

		// avoid "not fullscreen" warnings from vrmonitor
		vr::VRProperties()->SetBoolProperty( m_ulPropertyContainer, Prop_IsOnDesktop_Bool, m_displayOnDesktop);
		vr::VRProperties()->SetBoolProperty( m_ulPropertyContainer, Prop_HasDriverDirectModeComponent_Bool, false);
		//Debug mode activate Windowed Mode (borderless fullscreen), lock to 30 FPS 
		vr::VRProperties()->SetBoolProperty(m_ulPropertyContainer, Prop_DisplayDebugMode_Bool, m_bDebugMode);


		// Icons can be configured in code or automatically configured by an external file "drivername\resources\driver.vrresources".
		// Icon properties NOT configured in code (post Activate) are then auto-configured by the optional presence of a driver's "drivername\resources\driver.vrresources".
		// In this manner a driver can configure their icons in a flexible data driven fashion by using an external file.
		//
		// The structure of the driver.vrresources file allows a driver to specialize their icons based on their HW.
		// Keys matching the value in "Prop_ModelNumber_String" are considered first, since the driver may have model specific icons.
		// An absence of a matching "Prop_ModelNumber_String" then considers the ETrackedDeviceClass ("HMD", "Controller", "GenericTracker", "TrackingReference")
		// since the driver may have specialized icons based on those device class names.
		//
		// An absence of either then falls back to the "system.vrresources" where generic device class icons are then supplied.
		//
		// Please refer to "bin\drivers\sample\resources\driver.vrresources" which contains this sample configuration.
		//
		// "Alias" is a reserved key and specifies chaining to another json block.
		//
		// In this sample configuration file (overly complex FOR EXAMPLE PURPOSES ONLY)....
		//
		// "Model-v2.0" chains through the alias to "Model-v1.0" which chains through the alias to "Model-v Defaults".
		//
		// Keys NOT found in "Model-v2.0" would then chase through the "Alias" to be resolved in "Model-v1.0" and either resolve their or continue through the alias.
		// Thus "Prop_NamedIconPathDeviceAlertLow_String" in each model's block represent a specialization specific for that "model".
		// Keys in "Model-v Defaults" are an example of mapping to the same states, and here all map to "Prop_NamedIconPathDeviceOff_String".
	
	//	vr::VRProperties()->SetStringProperty( m_ulPropertyContainer, vr::Prop_NamedIconPathDeviceOff_String, "{oculus}/resources/icons/cv1_headset_off.png" );
	//	vr::VRProperties()->SetStringProperty( m_ulPropertyContainer, vr::Prop_NamedIconPathDeviceSearching_String, "{oculus}/resources/icons/cv1_headset_searching.b4bfb144.gif" );
	//	vr::VRProperties()->SetStringProperty( m_ulPropertyContainer, vr::Prop_NamedIconPathDeviceSearchingAlert_String, "{oculus}/resources/icons/cv1_headset_alert_searching.b4bfb144.gif" );
	//	vr::VRProperties()->SetStringProperty( m_ulPropertyContainer, vr::Prop_NamedIconPathDeviceReady_String, "{oculus}/resources/icons/cv1_headset_ready.b4bfb144.png" );
	//	vr::VRProperties()->SetStringProperty( m_ulPropertyContainer, vr::Prop_NamedIconPathDeviceReadyAlert_String, "{oculus}/resources/icons/cv1_headset_ready_alert.b4bfb144.png" );
	//	vr::VRProperties()->SetStringProperty( m_ulPropertyContainer, vr::Prop_NamedIconPathDeviceNotReady_String, "{oculus}/resources/icons/cv1_headset_error.b4bfb144.png" );
	//	vr::VRProperties()->SetStringProperty( m_ulPropertyContainer, vr::Prop_NamedIconPathDeviceStandby_String, "{oculus}/resources/icons/cv1_headset_standby.b4bfb144.png" );
	//	vr::VRProperties()->SetStringProperty( m_ulPropertyContainer, vr::Prop_NamedIconPathDeviceAlertLow_String, "{oculus}/resources/icons/headset_sample_status_ready_low.png" );

		return VRInitError_None;
	}

	virtual void Deactivate() 
	{
		HMDIndex_t = vr::k_unTrackedDeviceIndexInvalid;
	}

	virtual void EnterStandby()
	{
	}

	void *GetComponent( const char *pchComponentNameAndVersion )
	{
		if ( !_stricmp( pchComponentNameAndVersion, vr::IVRDisplayComponent_Version ) )
		{
			return (vr::IVRDisplayComponent*)this;
		}

		// override this to add a component to a driver
		return NULL;
	}

	virtual void PowerOff() 
	{
	}

	/** debug request from a client */
	virtual void DebugRequest( const char *pchRequest, char *pchResponseBuffer, uint32_t unResponseBufferSize ) 
	{
		if( unResponseBufferSize >= 1 )
			pchResponseBuffer[0] = 0;
	}

	virtual void GetWindowBounds( int32_t *pnX, int32_t *pnY, uint32_t *pnWidth, uint32_t *pnHeight ) 
	{
		*pnX = m_nWindowX;
		*pnY = m_nWindowY;
		*pnWidth = m_nWindowWidth;
		*pnHeight = m_nWindowHeight;
	}

	virtual bool IsDisplayOnDesktop() 
	{
		return m_displayOnDesktop;
	}

	virtual bool IsDisplayRealDisplay() 
	{
		return m_displayReal;
	}

	virtual void GetRecommendedRenderTargetSize( uint32_t *pnWidth, uint32_t *pnHeight ) 
	{
		*pnWidth = m_nRenderWidth;
		*pnHeight = m_nRenderHeight;
	}

	virtual void GetEyeOutputViewport( EVREye eEye, uint32_t *pnX, uint32_t *pnY, uint32_t *pnWidth, uint32_t *pnHeight ) 
	{
		/**pnY = 0;
				*pnWidth = m_nWindowWidth / 2;
				*pnHeight = m_nWindowHeight;

				if ( eEye == Eye_Left )
				{
					*pnX = 0;
				}
				else
				{
					*pnX = m_nWindowWidth / 2;
				}*/

		if (m_bStereoMode) {

			*pnY = m_nScreenOffsetY;
			*pnWidth = m_nWindowWidth / 2;
			*pnHeight = m_nWindowHeight;

			if (eEye == Eye_Left)
			{
				*pnX = m_nDistanceBetweenEyes + m_nScreenOffsetX;
			}
			else
			{
				*pnX = (m_nWindowWidth / 2) - m_nDistanceBetweenEyes + m_nScreenOffsetX;
			}
		}
		else { //Mono mode
			pnY = 0;
			*pnWidth = m_nRenderWidth;
			*pnHeight = m_nRenderHeight;

			if (eEye == Eye_Left)
			{
				*pnX = (m_nWindowWidth - m_nRenderWidth) / 2;
			}
			else
			{
				*pnX = m_nWindowWidth;
			}
			
	
		}
	}

	virtual void GetProjectionRaw( EVREye eEye, float *pfLeft, float *pfRight, float *pfTop, float *pfBottom ) 
	{
		if (m_bStereoMode) {
			
			*pfLeft = -m_fFOV;
			*pfRight = m_fFOV;
			*pfTop = -m_fFOV;
			*pfBottom = m_fFOV;
		}
		else { //Mono
			*pfLeft = (float)m_nRenderWidth / m_nRenderHeight * -1;
			*pfRight = (float)m_nRenderWidth / m_nRenderHeight;
			*pfTop = -1.0;
			*pfBottom = 1.0;
		}
	}

	virtual DistortionCoordinates_t ComputeDistortion( EVREye eEye, float fU, float fV ) 
	{
		DistortionCoordinates_t coordinates;

		float hX;
		float hY;
		double rr;
		double r2;
		double theta;

		rr = sqrt((fU - 0.5f)*(fU - 0.5f) + (fV - 0.5f)*(fV - 0.5f));
		r2 = rr * (1 + m_fDistortionK1 * (rr*rr) + m_fDistortionK2 * (rr*rr*rr*rr));
		theta = atan2(fU - 0.5f, fV - 0.5f);
		hX = sin(theta)*r2*m_fZoomWidth;
		hY = cos(theta)*r2*m_fZoomHeight;

		coordinates.rfBlue[0] = hX + 0.5f;
		coordinates.rfBlue[1] = hY + 0.5f;
		coordinates.rfGreen[0] = hX + 0.5f;
		coordinates.rfGreen[1] = hY + 0.5f;
		coordinates.rfRed[0] = hX + 0.5f;
		coordinates.rfRed[1] = hY + 0.5f;

		return coordinates;
	}

	virtual DriverPose_t GetPose() 
	{
		DriverPose_t pose = { 0 };

		if (HMDConnected) {
			pose.poseIsValid = true;
			pose.result = TrackingResult_Running_OK;
			pose.deviceIsConnected = true;
		}
		else
		{
			pose.poseIsValid = false;
			pose.result = TrackingResult_Uninitialized;
			pose.deviceIsConnected = false;
		}

		pose.qWorldFromDriverRotation = HmdQuaternion_Init(1, 0, 0, 0);
		pose.qDriverFromHeadRotation = HmdQuaternion_Init(1, 0, 0, 0);

		if (HMDConnected) {

			//hmd data
			dH.GetHMDData(&HMDdata);

			//Set head tracking rotation
			HmdQuaternion_t HMDQuat;
			HMDQuat.w = HMDdata.qW;
			HMDQuat.x = HMDdata.qX;
			HMDQuat.y = HMDdata.qY;
			HMDQuat.z = HMDdata.qZ;
			pose.qRotation = HMDQuat;
			//Set head position tracking
			pose.vecPosition[0] = HMDdata.X;
			pose.vecPosition[1] = HMDdata.Z;
			pose.vecPosition[2] = HMDdata.Y;
		}

		return pose;
	}
	

	void RunFrame()
	{
		// In a real driver, this should happen from some pose tracking thread.
		// The RunFrame interval is unspecified and can be very irregular if some other
		// driver blocks it for some periodic task.
		if ( HMDIndex_t != vr::k_unTrackedDeviceIndexInvalid )
		{
			vr::VRServerDriverHost()->TrackedDevicePoseUpdated( HMDIndex_t , GetPose(), sizeof( DriverPose_t ) );
		}
	}

	std::string GetSerialNumber() const { return m_sSerialNumber; }

private:
	vr::TrackedDeviceIndex_t HMDIndex_t;
	vr::PropertyContainerHandle_t m_ulPropertyContainer;

	std::string m_sSerialNumber;
	std::string m_sModelNumber;

	float realfreq;

	int32_t m_nWindowX;
	int32_t m_nWindowY;
	int32_t m_nWindowWidth;
	int32_t m_nWindowHeight;
	int32_t m_nRenderWidth;
	int32_t m_nRenderHeight;
	float m_flSecondsFromVsyncToPhotons;
	float m_flDisplayFrequency;
	float m_flIPD;
	float m_fDistortionK1;
	float m_fDistortionK2;
	float m_fZoomWidth;
	float m_fZoomHeight;
	float m_fFOV;
	int32_t m_nDistanceBetweenEyes;
	int32_t m_nScreenOffsetY;
	int32_t m_nScreenOffsetX;
	bool m_bStereoMode = true;
	bool m_bDebugMode;
	bool m_displayReal;
	bool m_displayOnDesktop;
};

//-----------------------------------------------------------------------------
// Purpose: Controller stuff goes on over here
//-----------------------------------------------------------------------------

class C_ControllerDriver : public vr::ITrackedDeviceServerDriver
{
	vr::VRInputComponentHandle_t m_skeletonHandle;
	int32_t ControllerIndex;
public:
	C_ControllerDriver()
	{
		Ctrl1Index_t = vr::k_unTrackedDeviceIndexInvalid;
		Ctrl2Index_t = vr::k_unTrackedDeviceIndexInvalid;
		m_ulPropertyContainer = vr::k_ulInvalidPropertyContainer;
		m_skeletonHandle = vr::k_ulInvalidInputComponentHandle;
	}

	virtual void SetControllerIndex(int32_t CtrlIndex)
	{
		ControllerIndex = CtrlIndex;
	}

	virtual ~C_ControllerDriver()
	{
	}

	virtual EVRInitError Activate( vr::TrackedDeviceIndex_t unObjectId )
	{
		DriverLog("[HadesVR] Initializing controller %d",ControllerIndex);
		switch (ControllerIndex)
		{
		case 1:

			for (size_t i = 0; i < fingerTracking::NUM_BONES; i++)
			{
				m_handBones[i] = fingerTracking::Pose_OpenRight[i];
			}

			Ctrl1Index_t = unObjectId;
			m_ulPropertyContainer = vr::VRProperties()->TrackedDeviceToPropertyContainer(Ctrl1Index_t);		
			break;
		case 2:

			for (size_t i = 0; i < fingerTracking::NUM_BONES; i++)
			{
				m_handBones[i] = fingerTracking::Pose_OpenLeft[i];
			}

			Ctrl2Index_t = unObjectId;
			m_ulPropertyContainer = vr::VRProperties()->TrackedDeviceToPropertyContainer(Ctrl2Index_t);
			break;
		}

		initDevice(controllerMode, ControllerIndex, m_ulPropertyContainer, m_compHaptic, m_skeletonHandle );

		return VRInitError_None;
	}

	virtual void Deactivate()
	{
		switch (ControllerIndex)
		{
		case 1:
			Ctrl1Index_t = vr::k_unTrackedDeviceIndexInvalid;
			break;
		case 2:
			Ctrl2Index_t = vr::k_unTrackedDeviceIndexInvalid;
			break;
		}
	}


	virtual void EnterStandby()
	{
	}

	void *GetComponent( const char *pchComponentNameAndVersion )
	{
		// override this to add a component to a driver
		return NULL;
	}

	virtual void PowerOff()
	{
	}

	/** debug request from a client */
	virtual void DebugRequest( const char *pchRequest, char *pchResponseBuffer, uint32_t unResponseBufferSize )
	{
		if ( unResponseBufferSize >= 1 )
			pchResponseBuffer[0] = 0;
	}

	virtual DriverPose_t GetPose()
	{
		DriverPose_t pose = { 0 };
		pose.poseIsValid = true;
		//pose.result = TrackingResult_Calibrating_OutOfRange;
		pose.result = TrackingResult_Running_OK;
		pose.deviceIsConnected = true;
		pose.poseTimeOffset = 0.035;	//holy shit thanks okawo

		pose.qWorldFromDriverRotation = HmdQuaternion_Init( 1, 0, 0, 0 );
		pose.qDriverFromHeadRotation = HmdQuaternion_Init( 1, 0, 0, 0 );

		//Controllers positions and rotations
		if (ControllerIndex == 1) {

			pose.vecPosition[0] = RightCtrl.X;
			pose.vecPosition[1] = RightCtrl.Z;
			pose.vecPosition[2] = RightCtrl.Y;

			//Velocity
			pose.vecVelocity[0] = (pose.vecPosition[0] - FirstCtrlLastPos[0]) * 1000 / max((int)deltaTime.count(), 1); 
			pose.vecVelocity[1] = (pose.vecPosition[1] - FirstCtrlLastPos[1]) * 1000 / max((int)deltaTime.count(), 1);
			pose.vecVelocity[2] = (pose.vecPosition[2] - FirstCtrlLastPos[2]) * 1000 / max((int)deltaTime.count(), 1);
			FirstCtrlLastPos[0] = pose.vecPosition[0];
			FirstCtrlLastPos[1] = pose.vecPosition[1];
			FirstCtrlLastPos[2] = pose.vecPosition[2];

			//Rotation first controller
			pose.qRotation = retquat(RightCtrl.qW, RightCtrl.qX, RightCtrl.qY, RightCtrl.qZ);

		} else { 
			//Controller2
			pose.vecPosition[0] = LeftCtrl.X;
			pose.vecPosition[1] = LeftCtrl.Z;
			pose.vecPosition[2] = LeftCtrl.Y;

			//Velocity
			pose.vecVelocity[0] = (pose.vecPosition[0] - SecondCtrlLastPos[0]) * 1000 / max((int)deltaTime.count(), 1); 
			pose.vecVelocity[1] = (pose.vecPosition[1] - SecondCtrlLastPos[1]) * 1000 / max((int)deltaTime.count(), 1);
			pose.vecVelocity[2] = (pose.vecPosition[2] - SecondCtrlLastPos[2]) * 1000 / max((int)deltaTime.count(), 1);
			SecondCtrlLastPos[0] = pose.vecPosition[0];
			SecondCtrlLastPos[1] = pose.vecPosition[1];
			SecondCtrlLastPos[2] = pose.vecPosition[2];

			pose.qRotation = retquat(LeftCtrl.qW, LeftCtrl.qX, LeftCtrl.qY, LeftCtrl.qZ);
		}

		return pose;
	}

	void RunFrame()
	{
		switch (ControllerIndex)
		{
		case 1:
			if (Ctrl1Index_t != vr::k_unTrackedDeviceIndexInvalid)
			{
				vr::VRServerDriverHost()->TrackedDevicePoseUpdated(Ctrl1Index_t, GetPose(), sizeof(DriverPose_t));
			}
			break;
		case 2:
			if (Ctrl2Index_t != vr::k_unTrackedDeviceIndexInvalid)
			{
				vr::VRServerDriverHost()->TrackedDevicePoseUpdated(Ctrl2Index_t, GetPose(), sizeof(DriverPose_t));
			}
			break;
		}
		updateFingerTracking(controllerMode, ControllerIndex, m_skeletonHandle, m_handBones);

		updateDevice(controllerMode, ControllerIndex);
	}

	void UpdateDeviceBattery() 
	{
		vr::VRProperties()->SetFloatProperty(vr::VRProperties()->TrackedDeviceToPropertyContainer(Ctrl1Index_t), vr::Prop_DeviceBatteryPercentage_Float, RightCtrl.vBat);
		vr::VRProperties()->SetFloatProperty(vr::VRProperties()->TrackedDeviceToPropertyContainer(Ctrl2Index_t), vr::Prop_DeviceBatteryPercentage_Float, LeftCtrl.vBat);
	}

	void ProcessEvent( const vr::VREvent_t & vrEvent )
	{
		switch ( vrEvent.eventType )
		{
		case vr::VREvent_Input_HapticVibration:
		{
			if ( vrEvent.data.hapticVibration.componentHandle == m_compHaptic )
			{
				// This is where you would send a signal to hardware to trigger actual haptic feedback
			}
		}
		break;
		}
	}

	std::string GetSerialNumber() const { 
		return getDeviceSerial(controllerMode, ControllerIndex);
	}

private:
	vr::TrackedDeviceIndex_t Ctrl1Index_t;
	vr::TrackedDeviceIndex_t Ctrl2Index_t;
	vr::PropertyContainerHandle_t m_ulPropertyContainer;
	
	vr::VRBoneTransform_t m_handBones[31];
	//vr::VRInputComponentHandle_t m_compA;
	//vr::VRInputComponentHandle_t m_compB;
	//vr::VRInputComponentHandle_t m_compC;
	vr::VRInputComponentHandle_t m_compHaptic;
	//std::string m_sSerialNumber;
	//std::string m_sModelNumber;
};

//-----------------------------------------------------------------------------
// Purpose: Tracker stuff goes on down here
//-----------------------------------------------------------------------------

class C_TrackerDriver : public vr::ITrackedDeviceServerDriver
{
	int32_t TrackerIndex;
	vr::VRInputComponentHandle_t m_skeletonHandle;
public:
	C_TrackerDriver()
	{
		TrackerWaist_t = vr::k_unTrackedDeviceIndexInvalid;
		TrackerLeftFoot_t = vr::k_unTrackedDeviceIndexInvalid;
		TrackerRightFoot_t = vr::k_unTrackedDeviceIndexInvalid;
		m_ulPropertyContainer = vr::k_ulInvalidPropertyContainer;
		m_skeletonHandle = vr::k_ulInvalidInputComponentHandle;
	}

	virtual void SetTrackerIndex(int32_t trckIndex)
	{
		TrackerIndex = trckIndex;
	}

	virtual ~C_TrackerDriver()
	{
	}

	virtual EVRInitError Activate(vr::TrackedDeviceIndex_t unObjectId)
	{
		DriverLog("[HadesVR] Initializing tracker %d", TrackerIndex);
		switch (TrackerIndex)
		{
		case 1:
			TrackerWaist_t = unObjectId;
			m_ulPropertyContainer = vr::VRProperties()->TrackedDeviceToPropertyContainer(TrackerWaist_t);
			break;
		case 2:
			TrackerLeftFoot_t = unObjectId;
			m_ulPropertyContainer = vr::VRProperties()->TrackedDeviceToPropertyContainer(TrackerLeftFoot_t);
			break;
		case 3:
			TrackerRightFoot_t = unObjectId;
			m_ulPropertyContainer = vr::VRProperties()->TrackedDeviceToPropertyContainer(TrackerRightFoot_t);
			break;
		}

		initDevice(10, TrackerIndex, m_ulPropertyContainer, m_compHaptic, m_skeletonHandle);

		return VRInitError_None;
	}

	virtual void Deactivate()
	{
		switch (TrackerIndex)
		{
		case 1:
			TrackerWaist_t = vr::k_unTrackedDeviceIndexInvalid;
			break;
		case 2:
			TrackerLeftFoot_t = vr::k_unTrackedDeviceIndexInvalid;
			break;
		case 3:
			TrackerRightFoot_t = vr::k_unTrackedDeviceIndexInvalid;
			break;
		}
	}


	virtual void EnterStandby()
	{
	}

	void* GetComponent(const char* pchComponentNameAndVersion)
	{
		// override this to add a component to a driver
		return NULL;
	}

	virtual void PowerOff()
	{
	}

	/** debug request from a client */
	virtual void DebugRequest(const char* pchRequest, char* pchResponseBuffer, uint32_t unResponseBufferSize)
	{
		if (unResponseBufferSize >= 1)
			pchResponseBuffer[0] = 0;
	}

	virtual DriverPose_t GetPose()
	{
		DriverPose_t pose = { 0 };
		//pose.poseIsValid = false;
		pose.poseIsValid = true;
		//pose.result = TrackingResult_Calibrating_OutOfRange;
		pose.result = TrackingResult_Running_OK;
		pose.deviceIsConnected = true;

		pose.qWorldFromDriverRotation = HmdQuaternion_Init(1, 0, 0, 0);
		pose.qDriverFromHeadRotation = HmdQuaternion_Init(1, 0, 0, 0);

		//Controllers positions and rotations
		switch (TrackerIndex)
		{
		case 1:
			//Waist Tracker
			pose.vecPosition[0] = 0;
			pose.vecPosition[1] = 0;
			pose.vecPosition[2] = 0;
			//velocity
			pose.vecVelocity[0] = (pose.vecPosition[0] - TrackerWaistLastPos[0]) * 1000 / max((int)deltaTime.count(), 1) / 3;
			pose.vecVelocity[1] = (pose.vecPosition[1] - TrackerWaistLastPos[1]) * 1000 / max((int)deltaTime.count(), 1) / 3;
			pose.vecVelocity[2] = (pose.vecPosition[2] - TrackerWaistLastPos[2]) * 1000 / max((int)deltaTime.count(), 1) / 3;
			TrackerWaistLastPos[0] = pose.vecPosition[0];
			TrackerWaistLastPos[1] = pose.vecPosition[1];
			TrackerWaistLastPos[2] = pose.vecPosition[2];
			//Rotation
			pose.qRotation = retquat(RightCtrl.qW, RightCtrl.qX, RightCtrl.qY, RightCtrl.qZ);
			break;
		case 2:
			//Left foot tracker
			pose.vecPosition[0] = 0;
			pose.vecPosition[1] = 0;
			pose.vecPosition[2] = 0;
			//velocity
			pose.vecVelocity[0] = (pose.vecPosition[0] - TrackerLeftFootLastPos[0]) * 1000 / max((int)deltaTime.count(), 1) / 3;
			pose.vecVelocity[1] = (pose.vecPosition[1] - TrackerLeftFootLastPos[1]) * 1000 / max((int)deltaTime.count(), 1) / 3;
			pose.vecVelocity[2] = (pose.vecPosition[2] - TrackerLeftFootLastPos[2]) * 1000 / max((int)deltaTime.count(), 1) / 3;
			TrackerLeftFootLastPos[0] = pose.vecPosition[0];
			TrackerLeftFootLastPos[1] = pose.vecPosition[1];
			TrackerLeftFootLastPos[2] = pose.vecPosition[2];
			//rotation
			pose.qRotation = retquat(LeftCtrl.qW, LeftCtrl.qX, LeftCtrl.qY, LeftCtrl.qZ);
			break;
		case 3:
			//Right foot tracker
			pose.vecPosition[0] = 0;
			pose.vecPosition[1] = 0;
			pose.vecPosition[2] = 0;
			//velocity
			pose.vecVelocity[0] = (pose.vecPosition[0] - TrackerRightFootLastPos[0]) * 1000 / max((int)deltaTime.count(), 1) / 3;
			pose.vecVelocity[1] = (pose.vecPosition[1] - TrackerRightFootLastPos[1]) * 1000 / max((int)deltaTime.count(), 1) / 3;
			pose.vecVelocity[2] = (pose.vecPosition[2] - TrackerRightFootLastPos[2]) * 1000 / max((int)deltaTime.count(), 1) / 3;
			TrackerRightFootLastPos[0] = pose.vecPosition[0];
			TrackerRightFootLastPos[1] = pose.vecPosition[1];
			TrackerRightFootLastPos[2] = pose.vecPosition[2];

			//rotation
			pose.qRotation = retquat(LeftCtrl.qW, LeftCtrl.qX, LeftCtrl.qY, LeftCtrl.qZ);
			break;
		}

		return pose;
	}

	void RunFrame()
	{
		switch (TrackerIndex)
		{
		case 1:
			if (TrackerWaist_t != vr::k_unTrackedDeviceIndexInvalid)
			{
				vr::VRServerDriverHost()->TrackedDevicePoseUpdated(TrackerWaist_t, GetPose(), sizeof(DriverPose_t));
			}
			break;
		case 2:
			if (TrackerLeftFoot_t != vr::k_unTrackedDeviceIndexInvalid)
			{
				vr::VRServerDriverHost()->TrackedDevicePoseUpdated(TrackerLeftFoot_t, GetPose(), sizeof(DriverPose_t));
			}
			break;
		case 3:
			if (TrackerRightFoot_t != vr::k_unTrackedDeviceIndexInvalid)
			{
				vr::VRServerDriverHost()->TrackedDevicePoseUpdated(TrackerRightFoot_t, GetPose(), sizeof(DriverPose_t));
			}
			break;
		}
	}

	void UpdateDeviceBattery()
	{
		vr::VRProperties()->SetFloatProperty(vr::VRProperties()->TrackedDeviceToPropertyContainer(TrackerWaist_t), vr::Prop_DeviceBatteryPercentage_Float, 1.f);
		vr::VRProperties()->SetFloatProperty(vr::VRProperties()->TrackedDeviceToPropertyContainer(TrackerLeftFoot_t), vr::Prop_DeviceBatteryPercentage_Float, 1.f);
		vr::VRProperties()->SetFloatProperty(vr::VRProperties()->TrackedDeviceToPropertyContainer(TrackerRightFoot_t), vr::Prop_DeviceBatteryPercentage_Float, 1.f);
	}

	void ProcessEvent(const vr::VREvent_t& vrEvent)
	{
		switch (vrEvent.eventType)
		{
		case vr::VREvent_Input_HapticVibration:
		{
			if (vrEvent.data.hapticVibration.componentHandle == m_compHaptic)
			{
				// This is where you would send a signal to hardware to trigger actual haptic feedback
			}
		}
		break;
		}
	}

	std::string GetSerialNumber() const {
		return getDeviceSerial(10, TrackerIndex);
	}

private:
	vr::TrackedDeviceIndex_t TrackerWaist_t;
	vr::TrackedDeviceIndex_t TrackerLeftFoot_t;
	vr::TrackedDeviceIndex_t TrackerRightFoot_t;

	vr::PropertyContainerHandle_t m_ulPropertyContainer;

	//vr::VRInputComponentHandle_t m_compA;
	//vr::VRInputComponentHandle_t m_compB;
	//vr::VRInputComponentHandle_t m_compC;
	vr::VRInputComponentHandle_t m_compHaptic;
	//std::string m_sSerialNumber;
	//std::string m_sModelNumber;
};

//-----------------------------------------------------------------------------
// Purpose: important server driver stuff over here
//-----------------------------------------------------------------------------
class CServerDriver_Sample: public IServerTrackedDeviceProvider
{
public:
	virtual EVRInitError Init( vr::IVRDriverContext *pDriverContext ) ;
	virtual void Cleanup() ;
	virtual const char * const *GetInterfaceVersions() { return vr::k_InterfaceVersions; }
	virtual void RunFrame() ;
	virtual bool ShouldBlockStandbyMode()  { return false; }
	virtual void EnterStandby()  {}
	virtual void LeaveStandby()  {}

private:

	void BatteryUpdateThread();
	static void BatteryUpdateThreadEnter(CServerDriver_Sample* ptr) {
		ptr->BatteryUpdateThread();
	}
	bool m_bBatteryUpdateThreadAlive;
	std::thread* m_ptBatteryUpdateThread;
	bool ctrlsEnabled = false, HMDEnabled = false, trackersEnabled = false;
	
	C_HMDDeviceDriver *m_pNullHmdLatest = nullptr;

	C_ControllerDriver *m_pControllerRight = nullptr;
	C_ControllerDriver *m_pControllerLeft = nullptr;

	C_TrackerDriver* m_pTrackerWaist = nullptr;
	C_TrackerDriver* m_pTrackerLeftFoot = nullptr;
	C_TrackerDriver* m_pTrackerRightFoot = nullptr;
};

CServerDriver_Sample g_serverDriverNull;

EVRInitError CServerDriver_Sample::Init( vr::IVRDriverContext *pDriverContext )
{
	VR_INIT_SERVER_DRIVER_CONTEXT( pDriverContext );
	InitDriverLog( vr::VRDriverLog() );

	//this is stupid
	ctrlsEnabled = vr::VRSettings()->GetBool(k_pch_Driver_Section, k_pch_Controller_Enable_Bool);
	controllerMode = vr::VRSettings()->GetInt32(k_pch_Driver_Section, k_pch_Controller_Mode_Int32);
	HMDEnabled = vr::VRSettings()->GetBool(k_pch_Driver_Section, k_pch_HMD_Enable_Bool);
	trackersEnabled = vr::VRSettings()->GetInt32(k_pch_Driver_Section, k_pch_Tracker_Enable_Bool);
	trackerMode = vr::VRSettings()->GetInt32(k_pch_Driver_Section, k_pch_Tracker_Mode_Int32);

	if (trackersEnabled) {
		DriverLog("[TRACKER] Trackers enabled!");
		if (trackerMode == 0) {
			DriverLog("[TRACKER] Tracker Mode: Full body");
		}
		else {
			DriverLog("[TRACKER] Tracker Mode: Waist");
		}
	}

	if (controllerMode > 9) { controllerMode = 0; }

	dH.StartData(vr::VRSettings()->GetInt32(k_pch_Driver_Section, k_pch_HID_PID_Int32), vr::VRSettings()->GetInt32(k_pch_Driver_Section, k_pch_HID_VID_Int32));

	DriverLog("[DataStream] HID value PID = %d , VID = %d\n", vr::VRSettings()->GetInt32(k_pch_Driver_Section, k_pch_HID_PID_Int32), vr::VRSettings()->GetInt32(k_pch_Driver_Section, k_pch_HID_VID_Int32));

	if (dH.HIDConnected)
	{
		if (HMDEnabled) {
			HMDConnected = true;
		}
		if (ctrlsEnabled) {
			ctrlsConnected = true;
		}
		if (trackersEnabled) {
			trackersConnected = true;
		}
	}
	else 
	{
		HMDConnected = false;
		ctrlsConnected = false;
		trackersConnected = false;
		return vr::VRInitError_Init_InterfaceNotFound;
	}

	if (HMDConnected) 
	{
		m_pNullHmdLatest = new C_HMDDeviceDriver();
		vr::VRServerDriverHost()->TrackedDeviceAdded(m_pNullHmdLatest->GetSerialNumber().c_str(), vr::TrackedDeviceClass_HMD, m_pNullHmdLatest);
	}

	if (ctrlsConnected) 
	{
		m_pControllerRight = new C_ControllerDriver();
		m_pControllerRight->SetControllerIndex(1);
		vr::VRServerDriverHost()->TrackedDeviceAdded(m_pControllerRight->GetSerialNumber().c_str(), vr::TrackedDeviceClass_Controller, m_pControllerRight);


		m_pControllerLeft = new C_ControllerDriver();
		m_pControllerLeft->SetControllerIndex(2);
		vr::VRServerDriverHost()->TrackedDeviceAdded(m_pControllerLeft->GetSerialNumber().c_str(), vr::TrackedDeviceClass_Controller, m_pControllerLeft);
	}

	if (trackersConnected) 
	{
		m_pTrackerWaist = new C_TrackerDriver();
		m_pTrackerWaist->SetTrackerIndex(1);
		vr::VRServerDriverHost()->TrackedDeviceAdded(m_pTrackerWaist->GetSerialNumber().c_str(), vr::TrackedDeviceClass_GenericTracker, m_pTrackerWaist);
		if (trackerMode == 0) {
			m_pTrackerLeftFoot = new C_TrackerDriver();
			m_pTrackerLeftFoot->SetTrackerIndex(2);
			vr::VRServerDriverHost()->TrackedDeviceAdded(m_pTrackerLeftFoot->GetSerialNumber().c_str(), vr::TrackedDeviceClass_GenericTracker, m_pTrackerLeftFoot);

			m_pTrackerRightFoot = new C_TrackerDriver();
			m_pTrackerRightFoot->SetTrackerIndex(3);
			vr::VRServerDriverHost()->TrackedDeviceAdded(m_pTrackerRightFoot->GetSerialNumber().c_str(), vr::TrackedDeviceClass_GenericTracker, m_pTrackerRightFoot);
		}
	}

	// battery thread
	m_bBatteryUpdateThreadAlive = true;
	m_ptBatteryUpdateThread = new std::thread(this->BatteryUpdateThreadEnter, this);
	if (!m_bBatteryUpdateThreadAlive) {
		return VRInitError_IPC_Failed;
	}

	return VRInitError_None;
}



void CServerDriver_Sample::Cleanup() 
{
	if (HMDConnected) {
		delete m_pNullHmdLatest;
		m_pNullHmdLatest = NULL;
	}

	if (ctrlsConnected) {
		delete m_pControllerRight;
		m_pControllerRight = NULL;
		delete m_pControllerLeft;
		m_pControllerLeft = NULL;
	}

	if (trackersConnected) {
		delete m_pTrackerWaist;
		m_pTrackerWaist = NULL;
		if (trackerMode == 0) {
			delete m_pTrackerLeftFoot;
			m_pTrackerLeftFoot = NULL;
			delete m_pTrackerRightFoot;
			m_pTrackerRightFoot = NULL;
		}
	}

	if (hDll != NULL) {
		FreeLibrary(hDll);
		hDll = nullptr;
	}

	if (dH.HIDConnected) {
		dH.HIDConnected = false;
		if (dH.pHIDthread) {
			dH.pHIDthread->join();
			delete dH.pHIDthread;
			dH.pHIDthread = nullptr;
			dH.stopData();
		}
	}
	if (dH.PSMConnected) {
		dH.PSMConnected = false;
		PSM_Shutdown();
		if (dH.pPSMUpdatethread) {
			dH.pPSMUpdatethread->join();
			delete dH.pPSMUpdatethread;
			dH.pPSMUpdatethread = nullptr;
		}
	}
	if (m_bBatteryUpdateThreadAlive) {
		m_bBatteryUpdateThreadAlive = false;
		if (m_ptBatteryUpdateThread) {
			m_ptBatteryUpdateThread->join();
			delete m_ptBatteryUpdateThread;
			m_ptBatteryUpdateThread = nullptr;
		}
	}

	CleanupDriverLog();
}

void CServerDriver_Sample::RunFrame()
{
	//Velocity
	static milliseconds lastMillis = duration_cast<milliseconds>(system_clock::now().time_since_epoch());
	deltaTime = duration_cast<milliseconds>(system_clock::now().time_since_epoch()) - lastMillis;
	lastMillis = duration_cast<milliseconds>(system_clock::now().time_since_epoch());

	if ( m_pNullHmdLatest )
	{
		m_pNullHmdLatest->RunFrame();
	}
	if (ctrlsConnected) 
	{
		dH.GetControllersData(&RightCtrl, &LeftCtrl);

		if (m_pControllerRight)
		{
			m_pControllerRight->RunFrame();
		}
		if (m_pControllerLeft)
		{
			m_pControllerLeft->RunFrame();
		}

		vr::VREvent_t vrEvent;
		while ( vr::VRServerDriverHost()->PollNextEvent( &vrEvent, sizeof( vrEvent ) ) )
		{
			if ( m_pControllerRight )
			{
				m_pControllerRight->ProcessEvent(vrEvent);
			}
			if (m_pControllerLeft)
			{
				m_pControllerLeft->ProcessEvent(vrEvent);
			}
		}
	}
	if (trackersConnected) 
	{
		if (m_pTrackerWaist) 
		{
			m_pTrackerWaist->RunFrame();
		}
		if (trackerMode == 0) {
			if (m_pTrackerLeftFoot)
			{
				m_pTrackerLeftFoot->RunFrame();
			}
			if (m_pTrackerRightFoot)
			{
				m_pTrackerRightFoot->RunFrame();
			}
		}

		vr::VREvent_t vrEvent;
		while (vr::VRServerDriverHost()->PollNextEvent(&vrEvent, sizeof(vrEvent)))
		{
			if (m_pTrackerWaist)
			{
				m_pTrackerWaist->ProcessEvent(vrEvent);
			}
			if (m_pTrackerLeftFoot)
			{
				m_pTrackerLeftFoot->ProcessEvent(vrEvent);
			}
			if (m_pTrackerRightFoot)
			{
				m_pTrackerRightFoot->ProcessEvent(vrEvent);
			}
		}
	}
}

void CServerDriver_Sample::BatteryUpdateThread() {
	
	while (m_bBatteryUpdateThreadAlive) 
	{
		//controllers
		if (m_pControllerRight)
		{
			m_pControllerRight->UpdateDeviceBattery();
		}
		if (m_pControllerLeft)
		{
			m_pControllerLeft->UpdateDeviceBattery();
		}
		//trackers
		if (m_pTrackerWaist) 
		{
			m_pTrackerWaist->UpdateDeviceBattery();
		}
		if (m_pTrackerLeftFoot)
		{
			m_pTrackerLeftFoot->UpdateDeviceBattery();
		}
		if (m_pTrackerRightFoot)
		{
			m_pTrackerRightFoot->UpdateDeviceBattery();
		}
		//night night
		std::this_thread::sleep_for(std::chrono::seconds(10));
	}
	m_bBatteryUpdateThreadAlive = false;
}

//-----------------------------------------------------------------------------
// Purpose:
//-----------------------------------------------------------------------------
HMD_DLL_EXPORT void *HmdDriverFactory( const char *pInterfaceName, int *pReturnCode )
{
	if( 0 == strcmp( IServerTrackedDeviceProvider_Version, pInterfaceName ) )
	{
		return &g_serverDriverNull;
	}
	/*if( 0 == strcmp( IVRWatchdogProvider_Version, pInterfaceName ) )
	{
		return &g_watchdogDriverNull;
	}*/

	if( pReturnCode )
		*pReturnCode = VRInitError_Init_InterfaceNotFound;

	return NULL;
}
