HadesVR/HadesVR/Software/Driver/src/samples/driver_HadesVR/include/driverlog.h

//========= Copyright Valve Corporation ============//

#ifndef DRIVERLOG_H
#define DRIVERLOG_H

#pragma once

#include <string>
#include "openvr/openvr_driver.h"

extern void DriverLog( const char *pchFormat, ... );


// --------------------------------------------------------------------------
// Purpose: Write to the log file only in debug builds
// --------------------------------------------------------------------------
extern void DebugDriverLog( const char *pchFormat, ... );


extern bool InitDriverLog( vr::IVRDriverLog *pDriverLog );
extern void CleanupDriverLog();



#endif // DRIVERLOG_H
