HadesVR/HadesVR/Software/Firmware/Experimental/Calibration/Calibration.ino

/*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
  The above copyright notice and this permission notice shall be included in all copies or substantial portions of the Software.

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
  =============================================================================
  ====================MPU-9250 ARDUINO AHRS CALIBRATION========================
  =============================================================================

  Part of the code is taken straight out of Kriswiner's MPU9250 AHRS.
  I've tested this on a 16mhz UNO and it runs fine, I have yet to test it on 12mhz and 8mhz.

  To calibrate the magnetometer all you have to do is upload this sketch and follow the instructions shown on the serial monitor.
  you can also calibrate the gyro and accel biases if you really want to, but it's not necessary, to do this you just need to comment out CALIBRATE_ONLY_MAG.

  Calibration settings are stored in the 328p's integrated EEPROM, if your MCU doesn't support EEPROM you'll have to comment the "USE_EEPROM" line, this will
  make it so that the calibration data is sent on the serial monitor and you'll have to input it manually.

  Anyways, check out Kriswiner's original MPU9250 code over here: https://github.com/kriswiner/MPU9250
  You can get the Madgwick filter from here: http://www.x-io.co.uk/open-source-imu-and-ahrs-algorithms/

  ~LiquidCGS
*/

#include <Wire.h>
#include "RegisterMap.h"
//==========================================================================================================
//************************************ USER CONFIGURABLE STUFF HERE*****************************************
//==========================================================================================================

#define MPU9250_ADDRESS 0x68 //ADO 0
#define CALIBRATE_ONLY_MAG    //comment this line if you want to calibrate accel and gyro biases.
#define USE_EEPROM            //comment this line if your MCU doesn't support EEPROM

//==========================================================================================================

#ifdef USE_EEPROM
#include <EEPROM.h>
#endif

float magCalibration[3]; // factory mag calibration

struct Calibration {
  int calDone;
  float magBias[3];
  float magScale[3]; // Bias corrections for mag
  float gyroBias[3]; // bias corrections
  float accelBias[3]; // bias corrections
};

Calibration cal;

float x, y, z;
static float ax, ay, az, gx, gy, gz, mx, my, mz;


enum class AFS { A2G, A4G, A8G, A16G };
enum class GFS { G250DPS, G500DPS, G1000DPS, G2000DPS };
enum class MFS { M14BITS, M16BITS }; // 0.6mG, 0.15mG per LSB

static float aRes;
static float gRes;
static float mRes;

AFS AFSSEL = AFS::A16G;
GFS GFSSEL = GFS::G2000DPS;
MFS MFSSEL = MFS::M16BITS;
#define Mmode 0x06                    // 2 for 8 Hz, 6 for 100 Hz continuous magnetometer data read

void setup() {

  Serial.begin(115200);
  while (!Serial) {
    ;
  }
  Wire.begin();

  aRes = getAres();
  gRes = getGres();
  mRes = getMres();

  if (readByte(MPU9250_ADDRESS, WHO_AM_I_MPU9250) == MPU9250_WHOAMI_DEFAULT_VALUE)
  {

    Serial.println("MPU9250 is online");
    initMPU();

    if (readByte(AK8963_ADDRESS, AK8963_WHO_AM_I) == AK8963_WHOAMI_DEFAULT_VALUE)
    {
      Serial.println("AK8963 is online");
      initAK8963(magCalibration);
    }
    else
    {
      Serial.print("Could not connect to AK8963: 0x");
      Serial.println(readByte(AK8963_ADDRESS, AK8963_WHO_AM_I), HEX);
    }
  }
  else
  {
    Serial.print("Could not connect to MPU9250: 0x");
    Serial.println(readByte(MPU9250_ADDRESS, WHO_AM_I_MPU9250), HEX);
  }


  Serial.println("Entered calibration mode!");

  delay(1000);

#ifndef CALIBRATE_ONLY_MAG
  Serial.println("Lay IMU on flat surface.");
  delay(10000);
  calibrateMPU9250(cal.gyroBias, cal.accelBias);
  Serial.println("AccelBias and GyroBias calibration done!");
  delay(1000);
#else
  cal.gyroBias[0] = 0;
  cal.gyroBias[1] = 0;
  cal.gyroBias[2] = 0;

  cal.accelBias[0] = 0;
  cal.accelBias[1] = 0;
  cal.accelBias[2] = 0;
#endif


  Serial.println("Magnetic calibration mode.");
  delay(1000);
  magcalMPU9250(cal.magBias, cal.magScale);

#ifdef USE_EEPROM
  Serial.println("Writting calibration values to EEPROM!");
  cal.calDone = 99;
  EEPROM.put(50, cal);
  delay(3000);
#else
  Serial.print("magBias: "); Serial.print(cal.magBias[0], 7); Serial.print(","); Serial.print(cal.magBias[1], 7); Serial.print(","); Serial.println(cal.magBias[2], 7);
  Serial.print("magScale: "); Serial.print(cal.magScale[0], 7); Serial.print(","); Serial.print(cal.magScale[1], 7); Serial.print(","); Serial.println(cal.magScale[2], 7);
  Serial.print("gyroBias: "); Serial.print(cal.gyroBias[0], 7); Serial.print(","); Serial.print(cal.gyroBias[1], 7); Serial.print(","); Serial.println(cal.gyroBias[2], 7);
  Serial.print("accelBias: "); Serial.print(cal.accelBias[0], 7); Serial.print(","); Serial.print(cal.accelBias[1], 7); Serial.print(","); Serial.println(cal.accelBias[2], 7);
#endif

}


void loop() {

}

void initMPU()
{
  // wake up device
  writeByte(MPU9250_ADDRESS, PWR_MGMT_1, 0x00); // Clear sleep mode bit (6), enable all sensors
  delay(100); // Wait for all registers to reset

  // get stable time source
  writeByte(MPU9250_ADDRESS, PWR_MGMT_1, 0x01);  // Auto select clock source to be PLL gyroscope reference if ready else
  delay(200);

  // Configure Gyro and Thermometer
  // Disable FSYNC and set thermometer and gyro bandwidth to 41 and 42 Hz, respectively;
  // minimum delay time for this setting is 5.9 ms, which means sensor fusion update rates cannot
  // be higher than 1 / 0.0059 = 170 Hz
  // DLPF_CFG = bits 2:0 = 011; this limits the sample rate to 1000 Hz for both
  // With the MPU9250, it is possible to get gyro sample rates of 32 kHz (!), 8 kHz, or 1 kHz
  writeByte(MPU9250_ADDRESS, MPU_CONFIG, 0x03);

  // Set sample rate = gyroscope output rate/(1 + SMPLRT_DIV)
  writeByte(MPU9250_ADDRESS, SMPLRT_DIV, 0x04);  // Use a 200 Hz rate; a rate consistent with the filter update rate
  // determined inset in CONFIG above

  // Set gyroscope full scale range
  // Range selects FS_SEL and GFS_SEL are 0 - 3, so 2-bit values are left-shifted into positions 4:3
  uint8_t c = readByte(MPU9250_ADDRESS, GYRO_CONFIG); // get current GYRO_CONFIG register value
  // c = c & ~0xE0; // Clear self-test bits [7:5]
  c = c & ~0x03; // Clear Fchoice bits [1:0]
  c = c & ~0x18; // Clear GFS bits [4:3]
  c = c | (uint8_t)GFSSEL << 3; // Set full scale range for the gyro
  // c =| 0x00; // Set Fchoice for the gyro to 11 by writing its inverse to bits 1:0 of GYRO_CONFIG
  writeByte(MPU9250_ADDRESS, GYRO_CONFIG, c ); // Write new GYRO_CONFIG value to register

  // Set accelerometer full-scale range configuration
  c = readByte(MPU9250_ADDRESS, ACCEL_CONFIG); // get current ACCEL_CONFIG register value
  // c = c & ~0xE0; // Clear self-test bits [7:5]
  c = c & ~0x18;  // Clear AFS bits [4:3]
  c = c | (uint8_t)AFSSEL << 3; // Set full scale range for the accelerometer
  writeByte(MPU9250_ADDRESS, ACCEL_CONFIG, c); // Write new ACCEL_CONFIG register value

  // Set accelerometer sample rate configuration
  // It is possible to get a 4 kHz sample rate from the accelerometer by choosing 1 for
  // accel_fchoice_b bit [3]; in this case the bandwidth is 1.13 kHz
  c = readByte(MPU9250_ADDRESS, ACCEL_CONFIG2); // get current ACCEL_CONFIG2 register value
  c = c & ~0x0F; // Clear accel_fchoice_b (bit 3) and A_DLPFG (bits [2:0])
  c = c | 0x03;  // Set accelerometer rate to 1 kHz and bandwidth to 41 Hz
  writeByte(MPU9250_ADDRESS, ACCEL_CONFIG2, c); // Write new ACCEL_CONFIG2 register value

  // The accelerometer, gyro, and thermometer are set to 1 kHz sample rates,
  // but all these rates are further reduced by a factor of 5 to 200 Hz because of the SMPLRT_DIV setting

  // Configure Interrupts and Bypass Enable
  // Set interrupt pin active high, push-pull, hold interrupt pin level HIGH until interrupt cleared,
  // clear on read of INT_STATUS, and enable I2C_BYPASS_EN so additional chips
  // can join the I2C bus and all can be controlled by the Arduino as master
  writeByte(MPU9250_ADDRESS, INT_PIN_CFG, 0x22);
  writeByte(MPU9250_ADDRESS, INT_ENABLE, 0x01);  // Enable data ready (bit 0) interrupt
  delay(100);
}

void initAK8963(float * destination)
{
  // First extract the factory calibration for each magnetometer axis
  uint8_t rawData[3];  // x/y/z gyro calibration data stored here
  writeByte(AK8963_ADDRESS, AK8963_CNTL, 0x00); // Power down magnetometer
  delay(10);
  writeByte(AK8963_ADDRESS, AK8963_CNTL, 0x0F); // Enter Fuse ROM access mode
  delay(10);
  readBytes(AK8963_ADDRESS, AK8963_ASAX, 3, &rawData[0]);  // Read the x-, y-, and z-axis calibration values
  destination[0] =  (float)(rawData[0] - 128) / 256. + 1.; // Return x-axis sensitivity adjustment values, etc.
  destination[1] =  (float)(rawData[1] - 128) / 256. + 1.;
  destination[2] =  (float)(rawData[2] - 128) / 256. + 1.;
  writeByte(AK8963_ADDRESS, AK8963_CNTL, 0x00); // Power down magnetometer
  delay(10);
  // Configure the magnetometer for continuous read and highest resolution
  // set Mscale bit 4 to 1 (0) to enable 16 (14) bit resolution in CNTL register,
  // and enable continuous mode data acquisition Mmode (bits [3:0]), 0010 for 8 Hz and 0110 for 100 Hz sample rates
  writeByte(AK8963_ADDRESS, AK8963_CNTL, (uint8_t)MFSSEL << 4 | Mmode); // Set magnetometer data resolution and sample ODR
  delay(10);

  //  Serial.println("Calibration values: ");
  //  Serial.print("X-Axis sensitivity adjustment value "); Serial.println(destination[0], 2);
  //  Serial.print("Y-Axis sensitivity adjustment value "); Serial.println(destination[1], 2);
  //  Serial.print("Z-Axis sensitivity adjustment value "); Serial.println(destination[2], 2);
  //  Serial.print("X-Axis sensitivity offset value "); Serial.println(cal.magBias[0], 2);
  //  Serial.print("Y-Axis sensitivity offset value "); Serial.println(cal.magBias[1], 2);
  //  Serial.print("Z-Axis sensitivity offset value "); Serial.println(cal.magBias[2], 2);
}

void updateAccelGyro()
{
  int16_t MPU9250Data[7];                                       // used to read all 14 bytes at once from the MPU9250 accel/gyro
  uint8_t rawData[14];                                          // x/y/z accel register data stored here

  readBytes(MPU9250_ADDRESS, ACCEL_XOUT_H, 14, &rawData[0]);    // Read the 14 raw data registers into data array

  MPU9250Data[0] = ((int16_t)rawData[0] << 8) | rawData[1] ;    // Turn the MSB and LSB into a signed 16-bit value
  MPU9250Data[1] = ((int16_t)rawData[2] << 8) | rawData[3] ;
  MPU9250Data[2] = ((int16_t)rawData[4] << 8) | rawData[5] ;
  MPU9250Data[3] = ((int16_t)rawData[6] << 8) | rawData[7] ;
  MPU9250Data[4] = ((int16_t)rawData[8] << 8) | rawData[9] ;
  MPU9250Data[5] = ((int16_t)rawData[10] << 8) | rawData[11] ;
  MPU9250Data[6] = ((int16_t)rawData[12] << 8) | rawData[13] ;

  // Now we'll calculate the accleration value into actual g's
  ax = (float)MPU9250Data[0] * aRes - cal.accelBias[0];              // get actual g value, this depends on scale being set
  ay = (float)MPU9250Data[1] * aRes - cal.accelBias[1];
  az = (float)MPU9250Data[2] * aRes - cal.accelBias[2];

  // Calculate the gyro value into actual degrees per second
  gx = (float)MPU9250Data[4] * gRes - cal.gyroBias[0];               // get actual gyro value, this depends on scale being set
  gy = (float)MPU9250Data[5] * gRes - cal.gyroBias[1];
  gz = (float)MPU9250Data[6] * gRes - cal.gyroBias[2];
}

void updateMag()
{
  if (readByte(AK8963_ADDRESS, AK8963_ST1) & 0x01) {             // wait for magnetometer data ready bit to be set
    int16_t magCount[3] = {0, 0, 0};                             // Stores the 16-bit signed magnetometer sensor output
    uint8_t rawData[7];                                          // x/y/z gyro register data, ST2 register stored here, must read ST2 at end of data acquisition
    readBytes(AK8963_ADDRESS, AK8963_XOUT_L, 7, &rawData[0]);    // Read the six raw data and ST2 registers sequentially into data array
    uint8_t c = rawData[6];                                      // End data read by reading ST2 register
    if (!(c & 0x08)) {                                           // Check if magnetic sensor overflow set, if not then report data
      magCount[0] = ((int16_t)rawData[1] << 8) | rawData[0];     // Turn the MSB and LSB into a signed 16-bit value
      magCount[1] = ((int16_t)rawData[3] << 8) | rawData[2];     // Data stored as little Endian
      magCount[2] = ((int16_t)rawData[5] << 8) | rawData[4];
    }

    // getMres();
    // Calculate the magnetometer values in milliGauss
    // Include factory calibration per data sheet and user environmental corrections

    mx = (float)(magCount[0] * mRes * magCalibration[0] - cal.magBias[0]) * cal.magScale[0];  // get actual magnetometer value, this depends on scale being set
    my = (float)(magCount[1] * mRes * magCalibration[1] - cal.magBias[1]) * cal.magScale[1];
    mz = (float)(magCount[2] * mRes * magCalibration[2] - cal.magBias[2]) * cal.magScale[2];
    //
    //    // Apply mag soft iron error compensation
    //    mx = x * cal.mag_softiron_matrix[0][0] + y * cal.mag_softiron_matrix[0][1] + z * cal.mag_softiron_matrix[0][2];
    //    my = x * cal.mag_softiron_matrix[1][0] + y * cal.mag_softiron_matrix[1][1] + z * cal.mag_softiron_matrix[1][2];
    //    mz = x * cal.mag_softiron_matrix[2][0] + y * cal.mag_softiron_matrix[2][1] + z * cal.mag_softiron_matrix[2][2];
  }
}

float getAres()
{
  switch (AFSSEL)
  {
    // Possible accelerometer scales (and their register bit settings) are:
    // 2 Gs (00), 4 Gs (01), 8 Gs (10), and 16 Gs  (11).
    // Here's a bit of an algorith to calculate DPS/(ADC tick) based on that 2-bit value:
    case AFS::A2G:  return 2.0 / 32768.0;
    case AFS::A4G:  return 4.0 / 32768.0;
    case AFS::A8G:  return 8.0 / 32768.0;
    case AFS::A16G: return 16.0 / 32768.0;
  }
}

float getGres()
{
  switch (GFSSEL)
  {
    // Possible gyro scales (and their register bit settings) are:
    // 250 DPS (00), 500 DPS (01), 1000 DPS (10), and 2000 DPS  (11).
    // Here's a bit of an algorith to calculate DPS/(ADC tick) based on that 2-bit value:
    case GFS::G250DPS:  return 250.0 / 32768.0;
    case GFS::G500DPS:  return 500.0 / 32768.0;
    case GFS::G1000DPS: return 1000.0 / 32768.0;
    case GFS::G2000DPS: return 2000.0 / 32768.0;
  }
}

float getMres()
{
  switch (MFSSEL)
  {
    // Possible magnetometer scales (and their register bit settings) are:
    // 14 bit resolution (0) and 16 bit resolution (1)
    // Proper scale to return milliGauss
    case MFS::M14BITS: return 10. * 4912. / 8190.0;
    case MFS::M16BITS: return 10. * 4912. / 32760.0;
  }
}

void calibrateMPU9250(float * dest1, float * dest2)
{
  uint8_t data[12]; // data array to hold accelerometer and gyro x, y, z, data
  uint16_t ii, packet_count, fifo_count;
  int32_t gyro_bias[3]  = {0, 0, 0}, accel_bias[3] = {0, 0, 0};

  // reset device
  writeByte(MPU9250_ADDRESS, PWR_MGMT_1, 0x80); // Write a one to bit 7 reset bit; toggle reset device
  delay(100);

  // get stable time source; Auto select clock source to be PLL gyroscope reference if ready
  // else use the internal oscillator, bits 2:0 = 001
  writeByte(MPU9250_ADDRESS, PWR_MGMT_1, 0x01);
  writeByte(MPU9250_ADDRESS, PWR_MGMT_2, 0x00);
  delay(200);

  // Configure device for bias calculation
  writeByte(MPU9250_ADDRESS, INT_ENABLE, 0x00);   // Disable all interrupts
  writeByte(MPU9250_ADDRESS, FIFO_EN, 0x00);      // Disable FIFO
  writeByte(MPU9250_ADDRESS, PWR_MGMT_1, 0x00);   // Turn on internal clock source
  writeByte(MPU9250_ADDRESS, I2C_MST_CTRL, 0x00); // Disable I2C master
  writeByte(MPU9250_ADDRESS, USER_CTRL, 0x00);    // Disable FIFO and I2C master modes
  writeByte(MPU9250_ADDRESS, USER_CTRL, 0x0C);    // Reset FIFO and DMP
  delay(15);

  // Configure MPU6050 gyro and accelerometer for bias calculation
  writeByte(MPU9250_ADDRESS, MPU_CONFIG, 0x01);      // Set low-pass filter to 188 Hz
  writeByte(MPU9250_ADDRESS, SMPLRT_DIV, 0x00);  // Set sample rate to 1 kHz
  writeByte(MPU9250_ADDRESS, GYRO_CONFIG, 0x00);  // Set gyro full-scale to 250 degrees per second, maximum sensitivity
  writeByte(MPU9250_ADDRESS, ACCEL_CONFIG, 0x00); // Set accelerometer full-scale to 2 g, maximum sensitivity

  uint16_t  gyrosensitivity  = 131;   // = 131 LSB/degrees/sec
  uint16_t  accelsensitivity = 16384;  // = 16384 LSB/g

  // Configure FIFO to capture accelerometer and gyro data for bias calculation
  writeByte(MPU9250_ADDRESS, USER_CTRL, 0x40);   // Enable FIFO
  writeByte(MPU9250_ADDRESS, FIFO_EN, 0x78);     // Enable gyro and accelerometer sensors for FIFO  (max size 512 bytes in MPU-9150)
  delay(40); // accumulate 40 samples in 40 milliseconds = 480 bytes

  // At end of sample accumulation, turn off FIFO sensor read
  writeByte(MPU9250_ADDRESS, FIFO_EN, 0x00);        // Disable gyro and accelerometer sensors for FIFO
  readBytes(MPU9250_ADDRESS, FIFO_COUNTH, 2, &data[0]); // read FIFO sample count
  fifo_count = ((uint16_t)data[0] << 8) | data[1];
  packet_count = fifo_count / 12;// How many sets of full gyro and accelerometer data for averaging

  for (ii = 0; ii < packet_count; ii++)
  {
    int16_t accel_temp[3] = {0, 0, 0}, gyro_temp[3] = {0, 0, 0};
    readBytes(MPU9250_ADDRESS, FIFO_R_W, 12, &data[0]); // read data for averaging
    accel_temp[0] = (int16_t) (((int16_t)data[0] << 8) | data[1]  ) ;  // Form signed 16-bit integer for each sample in FIFO
    accel_temp[1] = (int16_t) (((int16_t)data[2] << 8) | data[3]  ) ;
    accel_temp[2] = (int16_t) (((int16_t)data[4] << 8) | data[5]  ) ;
    gyro_temp[0]  = (int16_t) (((int16_t)data[6] << 8) | data[7]  ) ;
    gyro_temp[1]  = (int16_t) (((int16_t)data[8] << 8) | data[9]  ) ;
    gyro_temp[2]  = (int16_t) (((int16_t)data[10] << 8) | data[11]) ;

    accel_bias[0] += (int32_t) accel_temp[0]; // Sum individual signed 16-bit biases to get accumulated signed 32-bit biases
    accel_bias[1] += (int32_t) accel_temp[1];
    accel_bias[2] += (int32_t) accel_temp[2];
    gyro_bias[0]  += (int32_t) gyro_temp[0];
    gyro_bias[1]  += (int32_t) gyro_temp[1];
    gyro_bias[2]  += (int32_t) gyro_temp[2];
  }
  accel_bias[0] /= (int32_t) packet_count; // Normalize sums to get average count biases
  accel_bias[1] /= (int32_t) packet_count;
  accel_bias[2] /= (int32_t) packet_count;
  gyro_bias[0]  /= (int32_t) packet_count;
  gyro_bias[1]  /= (int32_t) packet_count;
  gyro_bias[2]  /= (int32_t) packet_count;

  if (accel_bias[2] > 0L) {
    accel_bias[2] -= (int32_t) accelsensitivity; // Remove gravity from the z-axis accelerometer bias calculation
  }
  else {
    accel_bias[2] += (int32_t) accelsensitivity;
  }

  // Construct the gyro biases for push to the hardware gyro bias registers, which are reset to zero upon device startup
  data[0] = (-gyro_bias[0] / 4  >> 8) & 0xFF; // Divide by 4 to get 32.9 LSB per deg/s to conform to expected bias input format
  data[1] = (-gyro_bias[0] / 4)       & 0xFF; // Biases are additive, so change sign on calculated average gyro biases
  data[2] = (-gyro_bias[1] / 4  >> 8) & 0xFF;
  data[3] = (-gyro_bias[1] / 4)       & 0xFF;
  data[4] = (-gyro_bias[2] / 4  >> 8) & 0xFF;
  data[5] = (-gyro_bias[2] / 4)       & 0xFF;

  // Push gyro biases to hardware registers
  writeByte(MPU9250_ADDRESS, XG_OFFSET_H, data[0]);
  writeByte(MPU9250_ADDRESS, XG_OFFSET_L, data[1]);
  writeByte(MPU9250_ADDRESS, YG_OFFSET_H, data[2]);
  writeByte(MPU9250_ADDRESS, YG_OFFSET_L, data[3]);
  writeByte(MPU9250_ADDRESS, ZG_OFFSET_H, data[4]);
  writeByte(MPU9250_ADDRESS, ZG_OFFSET_L, data[5]);

  // Output scaled gyro biases for display in the main program
  dest1[0] = (float) gyro_bias[0] / (float) gyrosensitivity;
  dest1[1] = (float) gyro_bias[1] / (float) gyrosensitivity;
  dest1[2] = (float) gyro_bias[2] / (float) gyrosensitivity;

  // Construct the accelerometer biases for push to the hardware accelerometer bias registers. These registers contain
  // factory trim values which must be added to the calculated accelerometer biases; on boot up these registers will hold
  // non-zero values. In addition, bit 0 of the lower byte must be preserved since it is used for temperature
  // compensation calculations. Accelerometer bias registers expect bias input as 2048 LSB per g, so that
  // the accelerometer biases calculated above must be divided by 8.

  // int32_t accel_bias_reg[3] = {0, 0, 0}; // A place to hold the factory accelerometer trim biases
  // readBytes(MPU9250_ADDRESS, XA_OFFSET_H, 2, &data[0]); // Read factory accelerometer trim values
  // accel_bias_reg[0] = (int32_t) (((int16_t)data[0] << 8) | data[1]);
  // readBytes(MPU9250_ADDRESS, YA_OFFSET_H, 2, &data[0]);
  // accel_bias_reg[1] = (int32_t) (((int16_t)data[0] << 8) | data[1]);
  // readBytes(MPU9250_ADDRESS, ZA_OFFSET_H, 2, &data[0]);
  // accel_bias_reg[2] = (int32_t) (((int16_t)data[0] << 8) | data[1]);

  // uint32_t mask = 1uL; // Define mask for temperature compensation bit 0 of lower byte of accelerometer bias registers
  // uint8_t mask_bit[3] = {0, 0, 0}; // Define array to hold mask bit for each accelerometer bias axis

  // for(ii = 0; ii < 3; ii++) {
  //     if((accel_bias_reg[ii] & mask)) mask_bit[ii] = 0x01; // If temperature compensation bit is set, record that fact in mask_bit
  // }

  // // Construct total accelerometer bias, including calculated average accelerometer bias from above
  // accel_bias_reg[0] -= (accel_bias[0] / 8); // Subtract calculated averaged accelerometer bias scaled to 2048 LSB/g (16 g full scale)
  // accel_bias_reg[1] -= (accel_bias[1] / 8);
  // accel_bias_reg[2] -= (accel_bias[2] / 8);

  // data[0] = (accel_bias_reg[0] >> 8) & 0xFF;
  // data[1] = (accel_bias_reg[0])      & 0xFF;
  // data[1] = data[1] | mask_bit[0]; // preserve temperature compensation bit when writing back to accelerometer bias registers
  // data[2] = (accel_bias_reg[1] >> 8) & 0xFF;
  // data[3] = (accel_bias_reg[1])      & 0xFF;
  // data[3] = data[3] | mask_bit[1]; // preserve temperature compensation bit when writing back to accelerometer bias registers
  // data[4] = (accel_bias_reg[2] >> 8) & 0xFF;
  // data[5] = (accel_bias_reg[2])      & 0xFF;
  // data[5] = data[5] | mask_bit[2]; // preserve temperature compensation bit when writing back to accelerometer bias registers

  // Apparently this is not working for the acceleration biases in the MPU-9250
  // Are we handling the temperature correction bit properly?
  // Push accelerometer biases to hardware registers
  // writeByte(MPU9250_ADDRESS, XA_OFFSET_H, data[0]);
  // writeByte(MPU9250_ADDRESS, XA_OFFSET_L, data[1]);
  // writeByte(MPU9250_ADDRESS, YA_OFFSET_H, data[2]);
  // writeByte(MPU9250_ADDRESS, YA_OFFSET_L, data[3]);
  // writeByte(MPU9250_ADDRESS, ZA_OFFSET_H, data[4]);
  // writeByte(MPU9250_ADDRESS, ZA_OFFSET_L, data[5]);

  // Output scaled accelerometer biases for display in the main program
  dest2[0] = (float)accel_bias[0] / (float)accelsensitivity;
  dest2[1] = (float)accel_bias[1] / (float)accelsensitivity;
  dest2[2] = (float)accel_bias[2] / (float)accelsensitivity;

  //  Serial.println("MPU9250 bias");
  //  Serial.println(" x   y   z  ");
  //  Serial.print((int)(1000 * cal.accelBias[0])); Serial.print(" ");
  //  Serial.print((int)(1000 * cal.accelBias[1])); Serial.print(" ");
  //  Serial.print((int)(1000 * cal.accelBias[2])); Serial.print(" ");
  //  Serial.println("mg");
  //  Serial.print(cal.gyroBias[0], 1); Serial.print(" ");
  //  Serial.print(cal.gyroBias[1], 1); Serial.print(" ");
  //  Serial.print(cal.gyroBias[2], 1); Serial.print(" ");
  //  Serial.println("o/s");

  delay(100);

  initMPU();

  delay(1000);
}

void magcalMPU9250(float * dest1, float * dest2)
{
  uint16_t ii = 0, sample_count = 0;
  int32_t mag_bias[3] = {0, 0, 0}, mag_scale[3] = {0, 0, 0};
  int16_t mag_max[3] = { -32767, -32767, -32767}, mag_min[3] = {32767, 32767, 32767}, mag_temp[3] = {0, 0, 0};

  Serial.println("Mag Calibration: Wave device in a figure eight until done!");
  delay(4000);

  // shoot for ~fifteen seconds of mag data
  if      (Mmode == 0x02) sample_count = 128;  // at 8 Hz ODR, new mag data is available every 125 ms
  else if (Mmode == 0x06) sample_count = 1500;  // at 100 Hz ODR, new mag data is available every 10 ms

  for (ii = 0; ii < sample_count; ii++)
  {
    uint8_t rawData[7];  // x/y/z gyro register data, ST2 register stored here, must read ST2 at end of data acquisition
    if (readByte(AK8963_ADDRESS, AK8963_ST1) & 0x01) { // wait for magnetometer data ready bit to be set
      readBytes(AK8963_ADDRESS, AK8963_XOUT_L, 7, &rawData[0]);  // Read the six raw data and ST2 registers sequentially into data array
      uint8_t c = rawData[6]; // End data read by reading ST2 register
      if (!(c & 0x08)) { // Check if magnetic sensor overflow set, if not then report data
        mag_temp[0] = ((int16_t)rawData[1] << 8) | rawData[0];  // Turn the MSB and LSB into a signed 16-bit value
        mag_temp[1] = ((int16_t)rawData[3] << 8) | rawData[2];  // Data stored as little Endian
        mag_temp[2] = ((int16_t)rawData[5] << 8) | rawData[4];
      }
    }
    for (int jj = 0; jj < 3; jj++)
    {
      if (mag_temp[jj] > mag_max[jj]) mag_max[jj] = mag_temp[jj];
      if (mag_temp[jj] < mag_min[jj]) mag_min[jj] = mag_temp[jj];
    }
    if (Mmode == 0x02) delay(135); // at 8 Hz ODR, new mag data is available every 125 ms
    if (Mmode == 0x06) delay(12); // at 100 Hz ODR, new mag data is available every 10 ms
  }
  //
  //  Serial.println("mag x min/max:"); Serial.println(mag_max[0]); Serial.println(mag_min[0]);
  //  Serial.println("mag y min/max:"); Serial.println(mag_max[1]); Serial.println(mag_min[1]);
  //  Serial.println("mag z min/max:"); Serial.println(mag_max[2]); Serial.println(mag_min[2]);

  // Get hard iron correction
  mag_bias[0]  = (mag_max[0] + mag_min[0]) / 2; // get average x mag bias in counts
  mag_bias[1]  = (mag_max[1] + mag_min[1]) / 2; // get average y mag bias in counts
  mag_bias[2]  = (mag_max[2] + mag_min[2]) / 2; // get average z mag bias in counts

  dest1[0] = (float) mag_bias[0] * mRes * magCalibration[0]; // save mag biases in G for main program
  dest1[1] = (float) mag_bias[1] * mRes * magCalibration[1];
  dest1[2] = (float) mag_bias[2] * mRes * magCalibration[2];

  // Get soft iron correction estimate
  mag_scale[0]  = (mag_max[0] - mag_min[0]) / 2; // get average x axis max chord length in counts
  mag_scale[1]  = (mag_max[1] - mag_min[1]) / 2; // get average y axis max chord length in counts
  mag_scale[2]  = (mag_max[2] - mag_min[2]) / 2; // get average z axis max chord length in counts

  float avg_rad = mag_scale[0] + mag_scale[1] + mag_scale[2];
  avg_rad /= 3.0;

  dest2[0] = avg_rad / ((float)mag_scale[0]);
  dest2[1] = avg_rad / ((float)mag_scale[1]);
  dest2[2] = avg_rad / ((float)mag_scale[2]);

  Serial.println("Mag Calibration done!");

  //  Serial.println("AK8963 mag biases (mG)");
  //  Serial.print(cal.magBias[0]); Serial.print(", ");
  //  Serial.print(cal.magBias[1]); Serial.print(", ");
  //  Serial.print(cal.magBias[2]); Serial.println();
  //  Serial.println("AK8963 mag scale (mG)");
  //  Serial.print(cal.magScale[0]); Serial.print(", ");
  //  Serial.print(cal.magScale[1]); Serial.print(", ");
  //  Serial.print(cal.magScale[2]); Serial.println();
}


bool dataAvailable()
{
  return (readByte(MPU9250_ADDRESS, INT_STATUS) & 0x01);
}

void writeByte(uint8_t address, uint8_t subAddress, uint8_t data)
{
  Wire.beginTransmission(address);  // Initialize the Tx buffer
  Wire.write(subAddress);           // Put slave register address in Tx buffer
  Wire.write(data);                 // Put data in Tx buffer
  Wire.endTransmission();           // Send the Tx buffer
}

uint8_t readByte(uint8_t address, uint8_t subAddress)
{
  uint8_t data; // `data` will store the register data
  Wire.beginTransmission(address);         // Initialize the Tx buffer
  Wire.write(subAddress);                  // Put slave register address in Tx buffer
  Wire.endTransmission(false);             // Send the Tx buffer, but send a restart to keep connection alive
  Wire.requestFrom(address, (uint8_t) 1);  // Read one byte from slave register address
  data = Wire.read();                      // Fill Rx buffer with result
  return data;                             // Return data read from slave register
}

void readBytes(uint8_t address, uint8_t subAddress, uint8_t count, uint8_t * dest)
{
  Wire.beginTransmission(address);   // Initialize the Tx buffer
  Wire.write(subAddress);            // Put slave register address in Tx buffer
  Wire.endTransmission(false);       // Send the Tx buffer, but send a restart to keep connection alive
  uint8_t i = 0;
  Wire.requestFrom(address, count);  // Read bytes from slave register address
  while (Wire.available()) {
    dest[i++] = Wire.read();
  }         // Put read results in the Rx buffer
}
