HadesVR/HadesVR/Software/Driver/src/samples/driver_HadesVR/src/HandTracking.cpp

/*

Original Work Copyright (c) 2021 LucidVR
Modified Work Copyright (c) 2021 HadesVR

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
THE SOFTWARE IS PROVIDED "AS IS", WITHOUT WARRANTY OF ANY KIND, EXPRESS OR
IMPLIED, INCLUDING BUT NOT LIMITED TO THE WARRANTIES OF MERCHANTABILITY,
FITNESS FOR A PARTICULAR PURPOSE AND NONINFRINGEMENT. IN NO EVENT SHALL THE
AUTHORS OR COPYRIGHT HOLDERS BE LIABLE FOR ANY CLAIM, DAMAGES OR OTHER
LIABILITY, WHETHER IN AN ACTION OF CONTRACT, TORT OR OTHERWISE, ARISING FROM,
OUT OF OR IN CONNECTION WITH THE SOFTWARE OR THE USE OR OTHER DEALINGS IN THE
SOFTWARE.
*/
//my crappy implementation of LucidVR's open vr gloves finger tracking code, check them out here https://github.com/LucidVR/opengloves-driver


#include "HandTracking.h"

namespace fingerTracking{

	vr::VRBoneTransform_t Pose_OpenRight[NUM_BONES] = {
	{ { 0.000000f,  0.000000f,  0.000000f,  1.000000f}, { 1.000000f, -0.000000f, -0.000000f,  0.000000f} },
	{ { 0.034038f,  0.036503f,  0.164722f,  1.000000f}, {-0.055147f, -0.078608f,  0.920279f, -0.379296f} },
	{ { 0.012083f,  0.028070f,  0.025050f,  1.000000f}, { 0.567418f, -0.464112f,  0.623374f, -0.272106f} },
	{ {-0.040406f, -0.000000f,  0.000000f,  1.000000f}, { 0.994838f,  0.082939f,  0.019454f,  0.055130f} },
	{ {-0.032517f, -0.000000f, -0.000000f,  1.000000f}, { 0.974793f, -0.003213f,  0.021867f, -0.222015f} },
	{ {-0.030464f,  0.000000f,  0.000000f,  1.000000f}, { 1.000000f, -0.000000f, -0.000000f,  0.000000f} },
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
	{ { 0.029874f,  0.000000f,  0.000000f,  1.000000f}, { 0.702185f, -0.006716f, -0.009289f,  0.711903f} },
	{ { 0.017979f,  0.000000f,  0.000000f,  1.000000f}, { 0.676853f,  0.007956f,  0.009917f,  0.736009f} },
	{ { 0.018018f,  0.000000f, -0.000000f,  1.000000f}, { 1.000000f,  0.000000f,  0.000000f,  0.000000f} },
	{ { 0.019716f,  0.002802f,  0.093937f,  1.000000f}, { 0.377286f, -0.540831f,  0.150446f, -0.736562f} },
	{ { 0.000171f,  0.016473f,  0.096515f,  1.000000f}, {-0.006456f,  0.022747f, -0.932927f, -0.359287f} },
	{ { 0.000448f,  0.001536f,  0.116543f,  1.000000f}, {-0.039357f,  0.105143f, -0.928833f, -0.353079f} },
	{ { 0.003949f, -0.014869f,  0.130608f,  1.000000f}, {-0.055071f,  0.068695f, -0.944016f, -0.317933f} },
	{ { 0.003263f, -0.034685f,  0.139926f,  1.000000f}, { 0.019690f, -0.100741f, -0.957331f, -0.270149f} },
	};

	float Lerp(const float a, const float b, const float f) {
		return a + f * (b - a);
	}

	void CalculateHandBones(vr::VRBoneTransform_t* HandBoneTransform, float thumbFingerFlexion, float indexFingerFlexion, float middleFingerFlexion, float ringFingerFlexion, float pinkyFingerFlexion, const bool isRightHand, int i){

		vr::VRBoneTransform_t* Pose_open;
		vr::VRBoneTransform_t* Pose_closed;
		float FlexionAmount;

		if (isRightHand)
		{
			Pose_open = Pose_OpenRight;
			Pose_closed = Pose_ClosedRight;
		}
		else 
		{
			Pose_open = Pose_OpenLeft;
			Pose_closed = Pose_ClosedLeft;
		}


		switch (i) 
		{
		case eBone_Aux_Thumb:
		case eBone_Thumb0:
		case eBone_Thumb1:
		case eBone_Thumb2:
		case eBone_Thumb3:
			FlexionAmount = thumbFingerFlexion;
			break;
		case eBone_Aux_IndexFinger:
		case eBone_IndexFinger0:
		case eBone_IndexFinger1:
		case eBone_IndexFinger2:
		case eBone_IndexFinger3:
		case eBone_IndexFinger4:
			FlexionAmount = indexFingerFlexion;
			break;
		case eBone_Aux_MiddleFinger:
		case eBone_MiddleFinger0:
		case eBone_MiddleFinger1:
		case eBone_MiddleFinger2:
		case eBone_MiddleFinger3:
		case eBone_MiddleFinger4:
			FlexionAmount = middleFingerFlexion;
			break;
		case eBone_Aux_RingFinger:
		case eBone_RingFinger0:
		case eBone_RingFinger1:
		case eBone_RingFinger2:
		case eBone_RingFinger3:
		case eBone_RingFinger4:
			FlexionAmount = ringFingerFlexion;
			break;
		case eBone_Aux_PinkyFinger:
		case eBone_PinkyFinger0:
		case eBone_PinkyFinger1:
		case eBone_PinkyFinger2:
		case eBone_PinkyFinger3:
		case eBone_PinkyFinger4:
			FlexionAmount = pinkyFingerFlexion;
			break;

		default:
			FlexionAmount = 0;
			return;
			break;
		}

		HandBoneTransform->orientation.w = Lerp(Pose_open[i].orientation.w, Pose_closed[i].orientation.w, FlexionAmount);
		HandBoneTransform->orientation.x = Lerp(Pose_open[i].orientation.x, Pose_closed[i].orientation.x, FlexionAmount);
		HandBoneTransform->orientation.y = Lerp(Pose_open[i].orientation.y, Pose_closed[i].orientation.y, FlexionAmount);
		HandBoneTransform->orientation.z = Lerp(Pose_open[i].orientation.z, Pose_closed[i].orientation.z, FlexionAmount);

		HandBoneTransform->position.v[0] = Lerp(Pose_open[i].position.v[0], Pose_closed[i].position.v[0], FlexionAmount);
		HandBoneTransform->position.v[1] = Lerp(Pose_open[i].position.v[1], Pose_closed[i].position.v[1], FlexionAmount);
		HandBoneTransform->position.v[2] = Lerp(Pose_open[i].position.v[2], Pose_closed[i].position.v[2], FlexionAmount);
		HandBoneTransform->position.v[3] = Lerp(Pose_open[i].position.v[3], Pose_closed[i].position.v[3], FlexionAmount);
		
	}
}
